UnbDroid/Open2017/Codigos/Vision/src/001.png

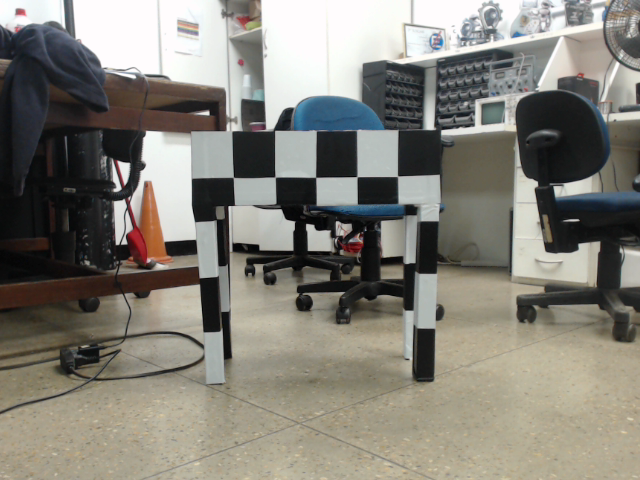
Codigos/Vision/src/001.png
