UnbDroid/Open2017/Codigos/Vision/src/003.png

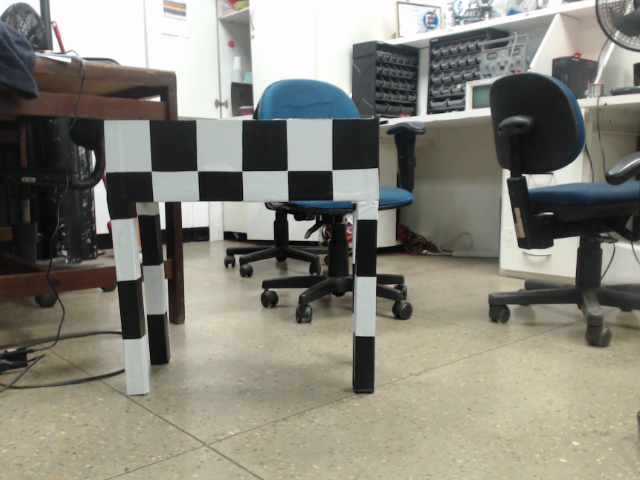
Codigos/Vision/src/003.png
