UnbDroid/Open2017/Codigos/Vision/src/004.png

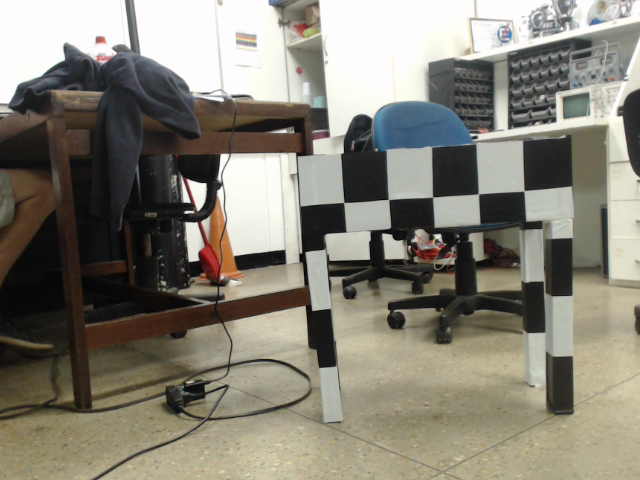
Codigos/Vision/src/004.png
