UnbDroid/Open2017/Codigos/Vision/src/005.png

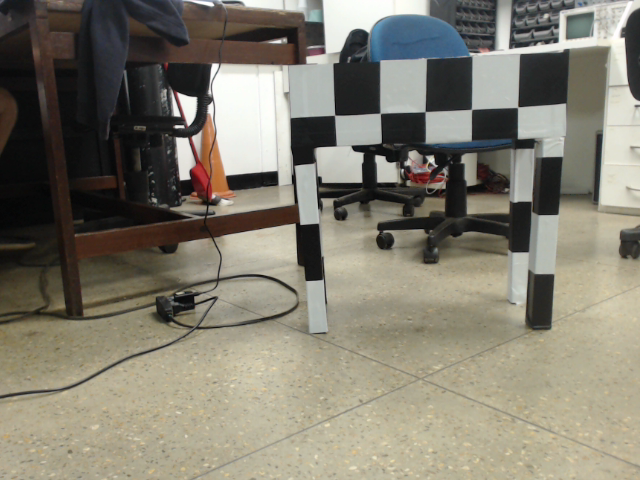
Codigos/Vision/src/005.png
