UnbDroid/Open2017/Codigos/Vision/src/006.png

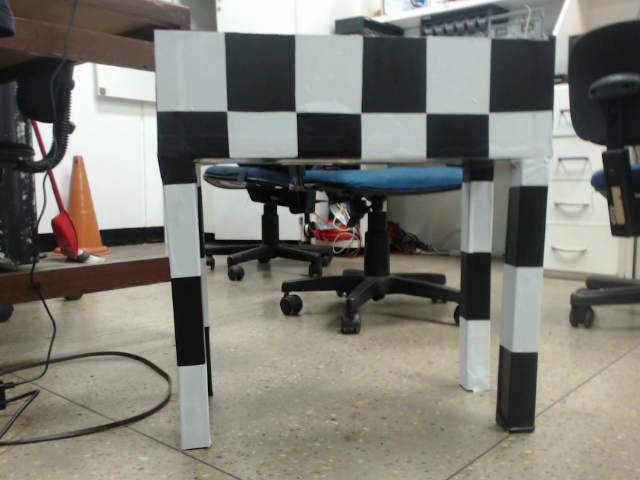
Codigos/Vision/src/006.png
