UnbDroid/Open2017/Codigos/Vision/src/007.png

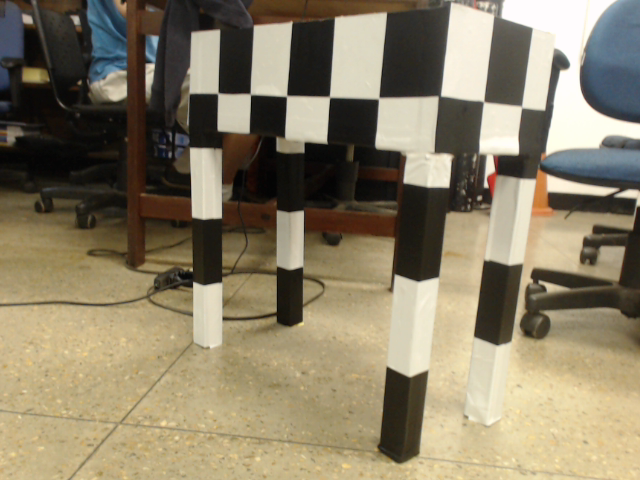
Codigos/Vision/src/007.png
