UnbDroid/Open2017/Codigos/Vision/src/008.png

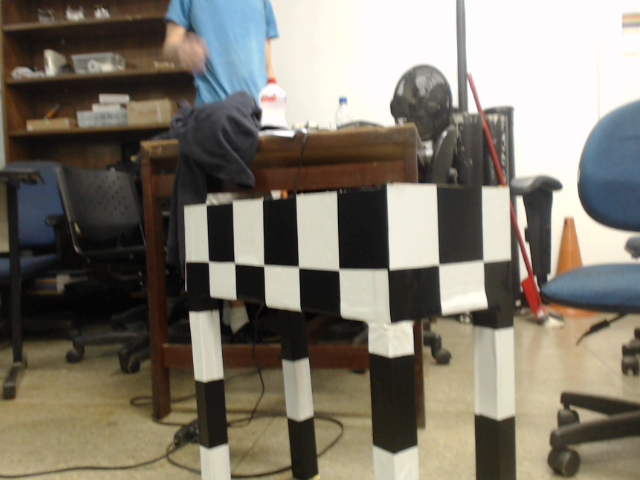
Codigos/Vision/src/008.png
