UnbDroid/Open2017/Codigos/Vision/src/009.png

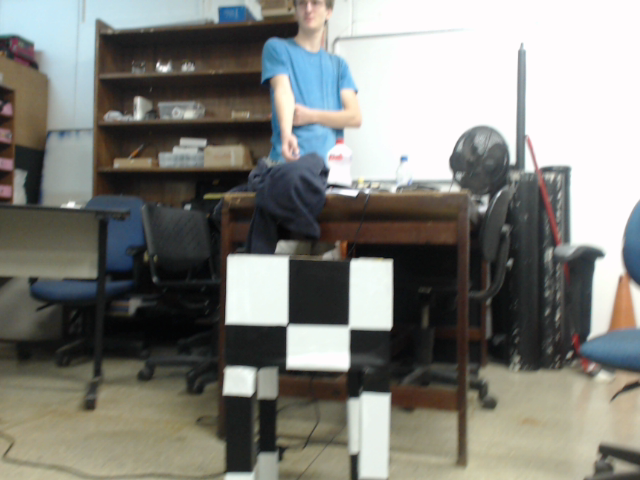
Codigos/Vision/src/009.png
