UnbDroid/Open2017/Codigos/Vision/src/010.png

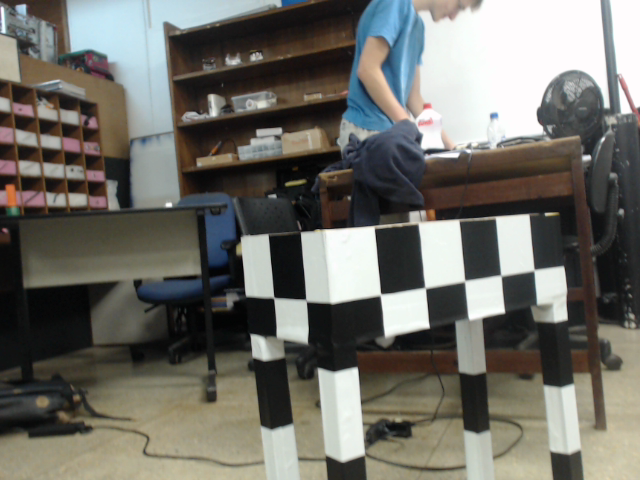
Codigos/Vision/src/010.png
