UnbDroid/Open2017/Codigos/Vision/src/011.png

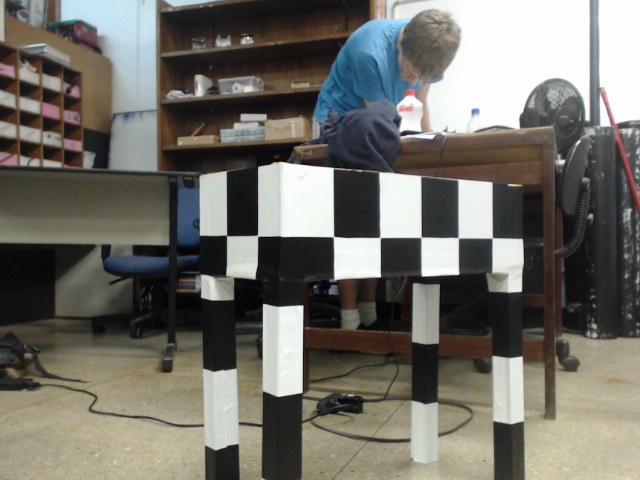
Codigos/Vision/src/011.png
