UnbDroid/Open2017/Codigos/Vision/src/012.png

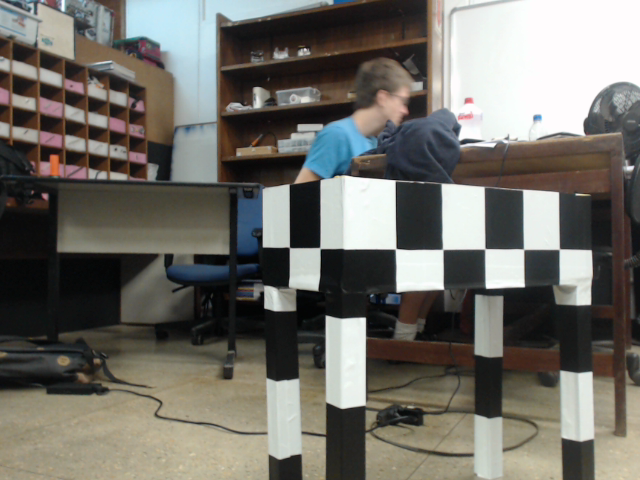
Codigos/Vision/src/012.png
