UnbDroid/Open2017/Codigos/Vision/src/013.png

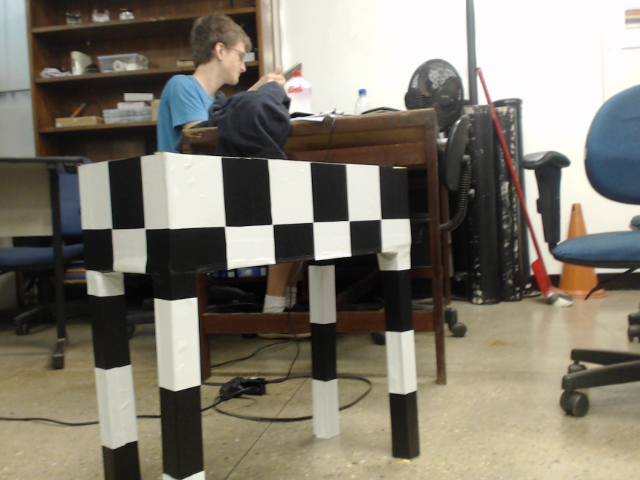
Codigos/Vision/src/013.png
