UnbDroid/Open2017/Codigos/Vision/src/014.png

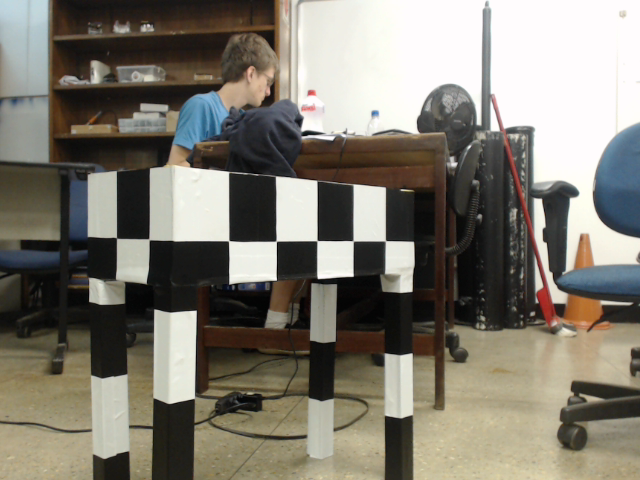
Codigos/Vision/src/014.png
