UnbDroid/Open2017/Codigos/Vision/src/015.png

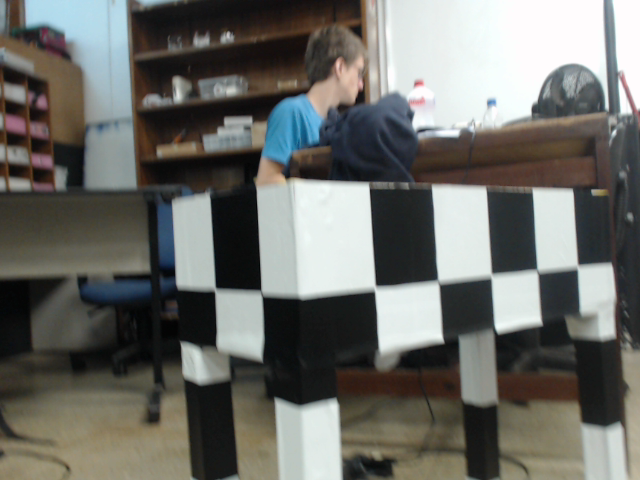
Codigos/Vision/src/015.png
