UnbDroid/Open2017/Codigos/Vision/src/016.png

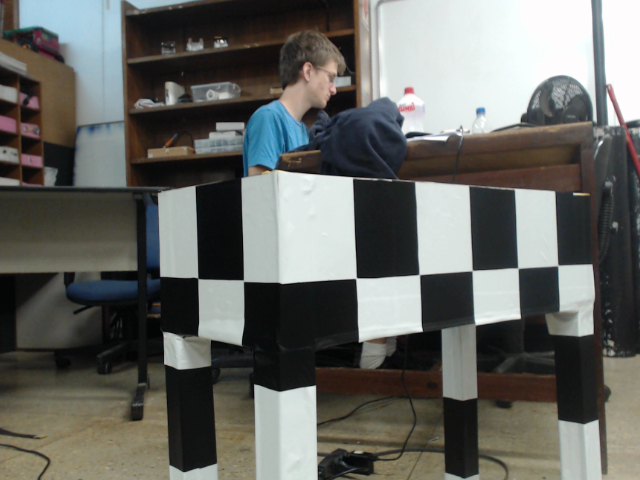
Codigos/Vision/src/016.png
