UnbDroid/Open2017/Codigos/Vision/src/017.png

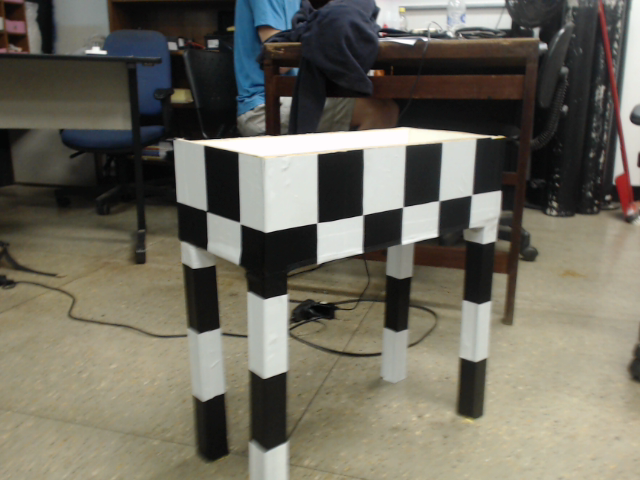
Codigos/Vision/src/017.png
