UnbDroid/Open2017/Codigos/Vision/src/018.png

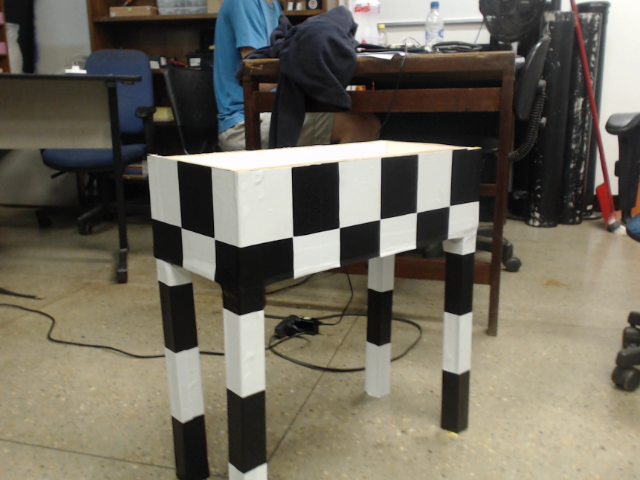
Codigos/Vision/src/018.png
