UnbDroid/Open2017/Codigos/Vision/src/019.png

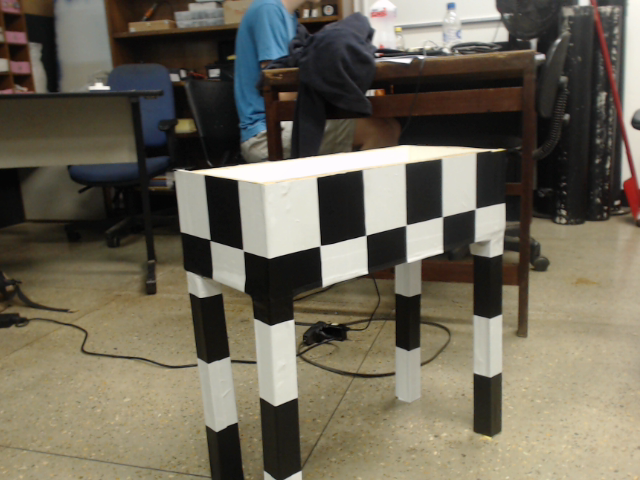
Codigos/Vision/src/019.png
