UnbDroid/Open2017/Codigos/Vision/src/020.png

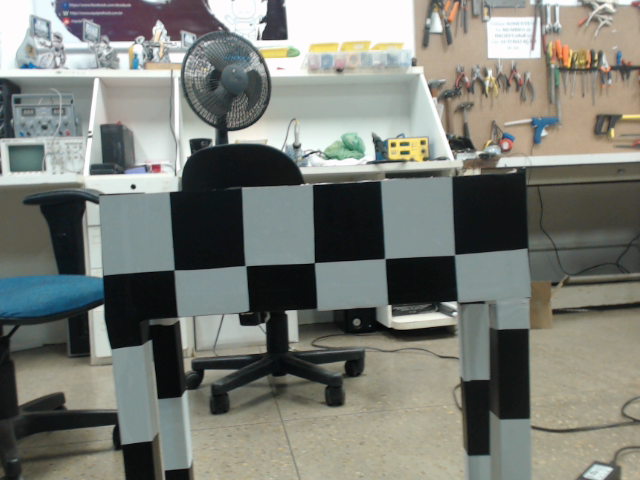
Codigos/Vision/src/020.png
