UnbDroid/Open2017/Codigos/Vision/src/021.png

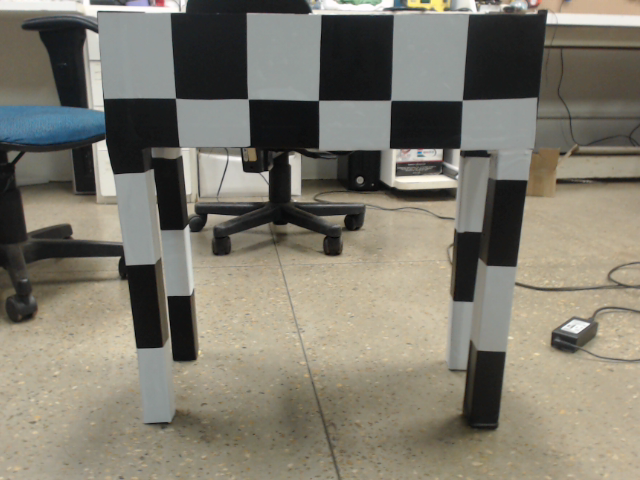
Codigos/Vision/src/021.png
