UnbDroid/Open2017/Codigos/Vision/src/022.png

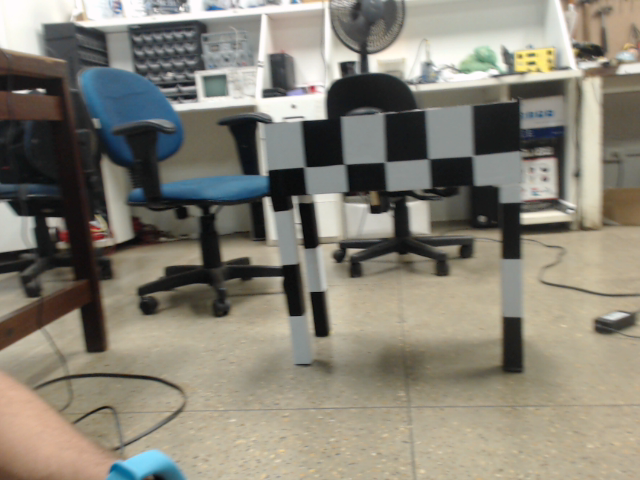
Codigos/Vision/src/022.png
