UnbDroid/Open2017/Codigos/Vision/src/023.png

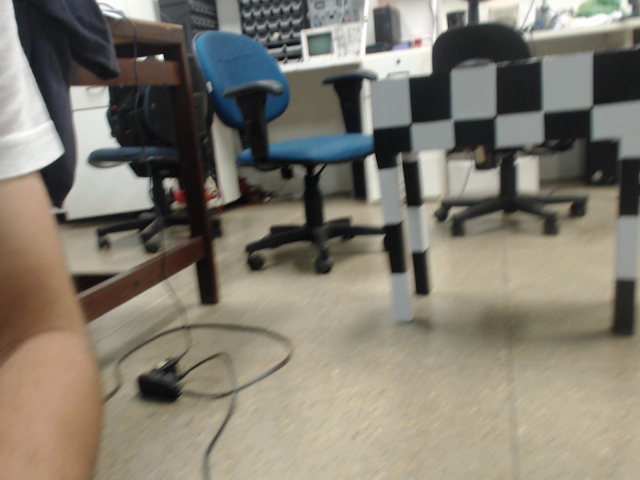
Codigos/Vision/src/023.png
