UnbDroid/Open2017/Codigos/Vision/src/024.png

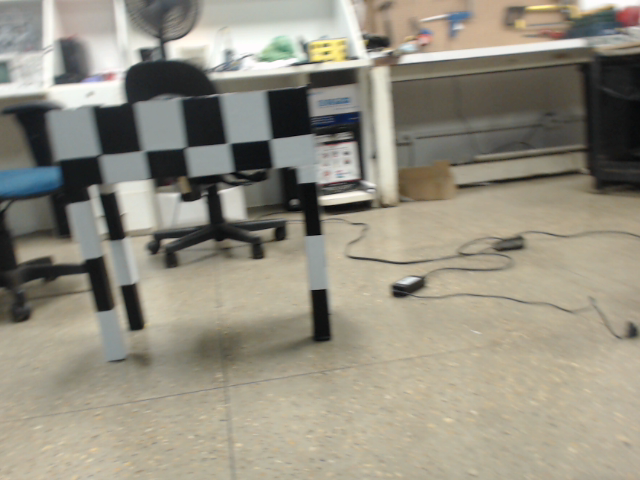
Codigos/Vision/src/024.png
