UnbDroid/Open2017/Codigos/Vision/src/026.png

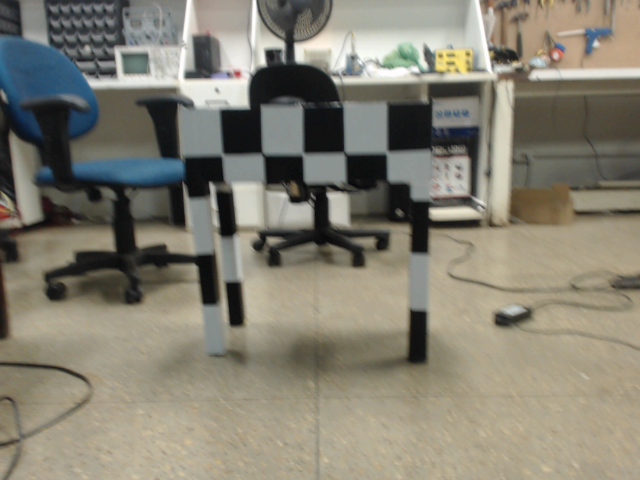
Codigos/Vision/src/026.png
