UnbDroid/Open2017/Codigos/Vision/src/027.png

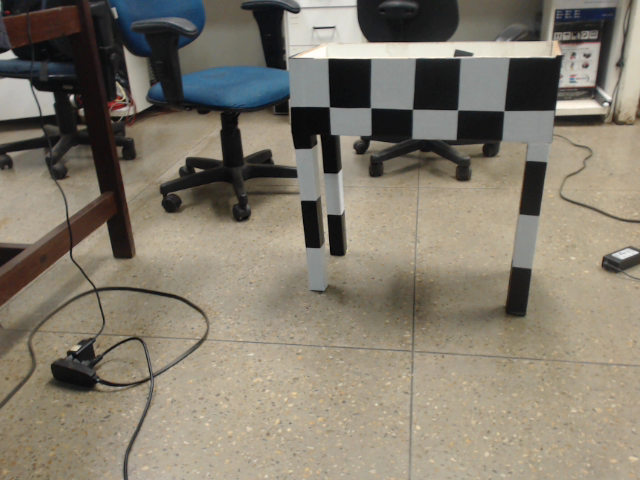
Codigos/Vision/src/027.png
