UnbDroid/Open2017/Codigos/Vision/src/028.png

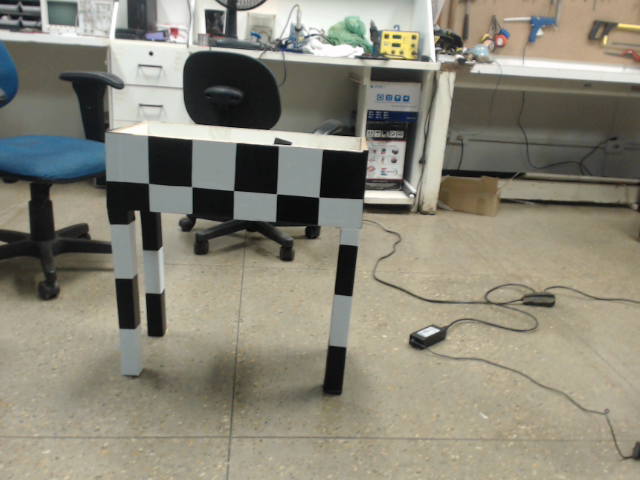
Codigos/Vision/src/028.png
