UnbDroid/Open2017/Codigos/Vision/src/029.png

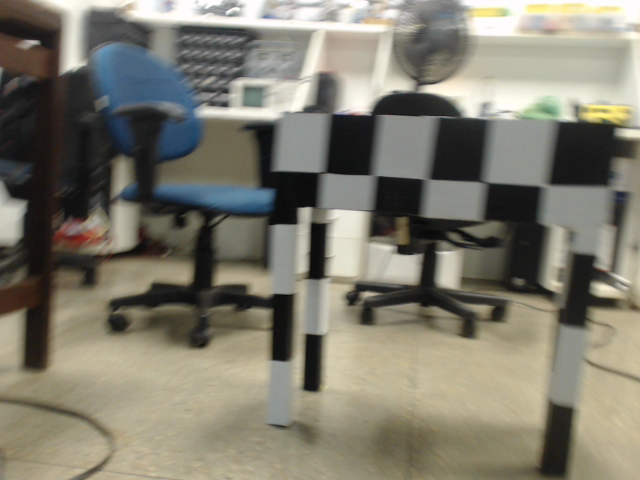
Codigos/Vision/src/029.png
