UnbDroid/Open2017/Codigos/Vision/src/030.png

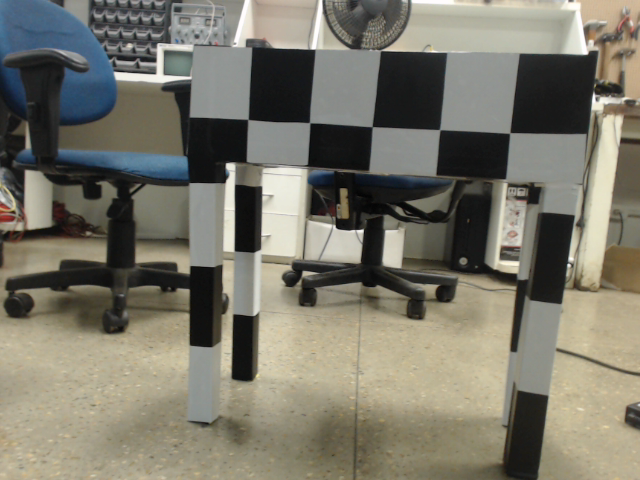
Codigos/Vision/src/030.png
