UnbDroid/Open2017/Codigos/Vision/src/031.png

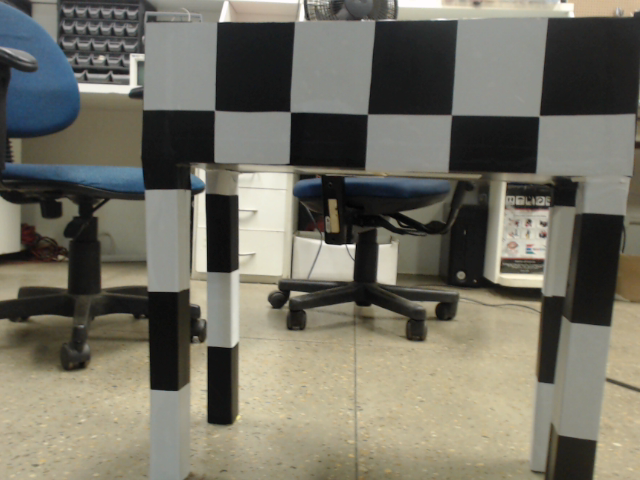
Codigos/Vision/src/031.png
