UnbDroid/Open2017/Codigos/Vision/src/032.png

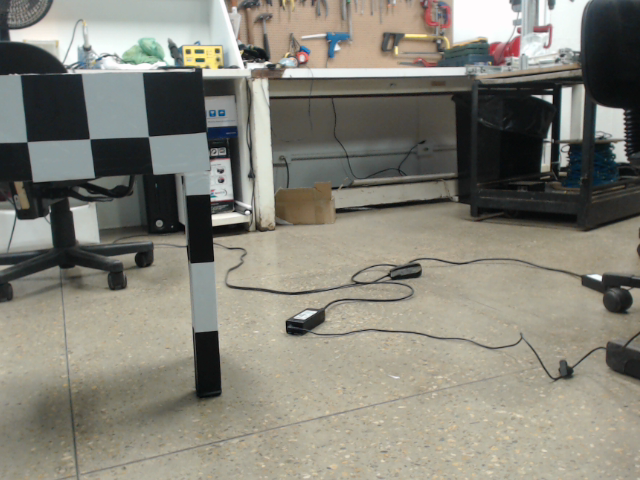
Codigos/Vision/src/032.png
