UnbDroid/Open2017/Codigos/Vision/src/033.png

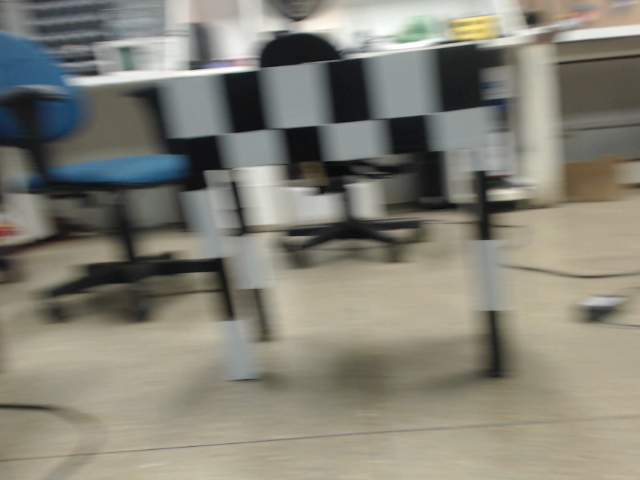
Codigos/Vision/src/033.png
