UnbDroid/Open2017/Codigos/Vision/src/034.png

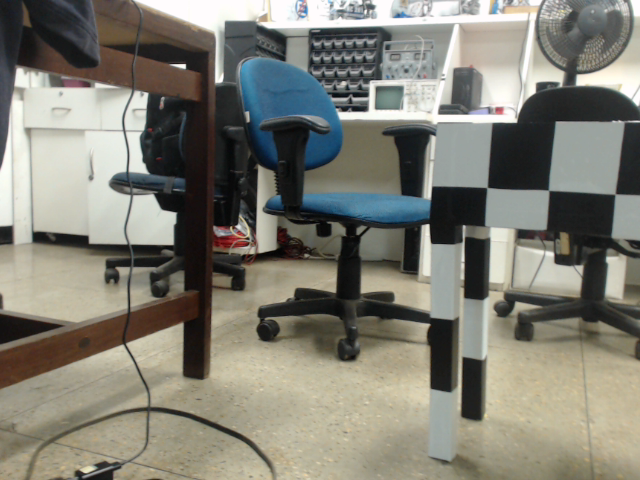
Codigos/Vision/src/034.png
