UnbDroid/Open2017/Codigos/Vision/src/035.png

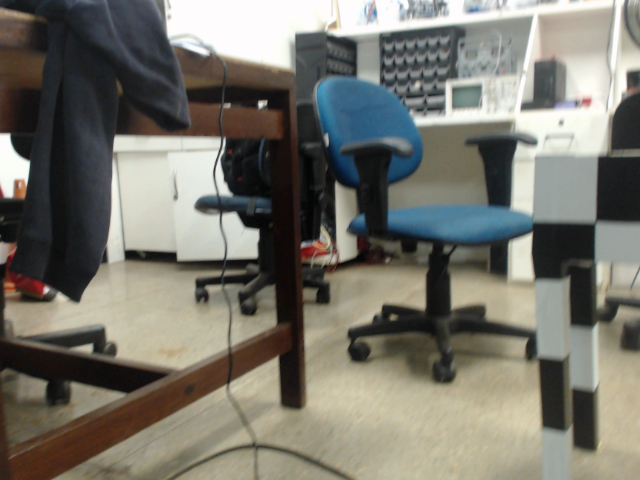
Codigos/Vision/src/035.png
