UnbDroid/Open2017/Codigos/Vision/src/036.png

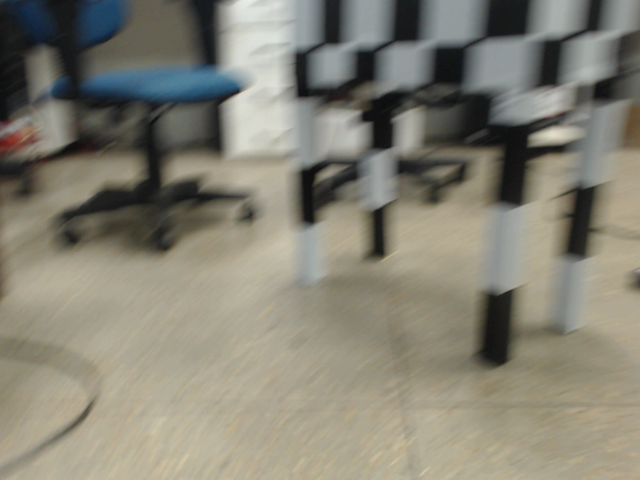
Codigos/Vision/src/036.png
