UnbDroid/Open2017/Codigos/Vision/src/037.png

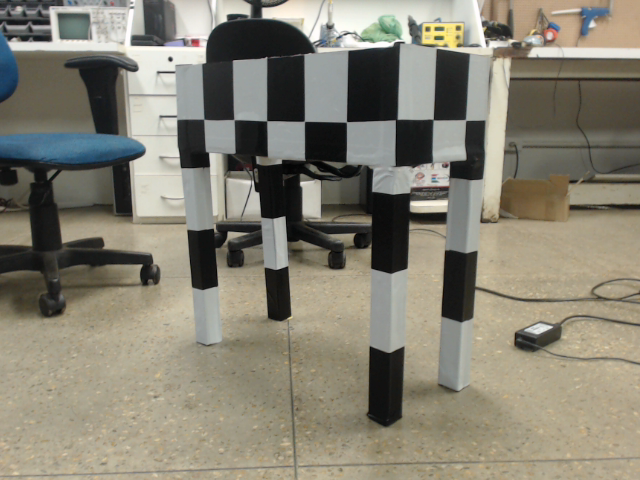
Codigos/Vision/src/037.png
