UnbDroid/Open2017/Codigos/Vision/src/038.png

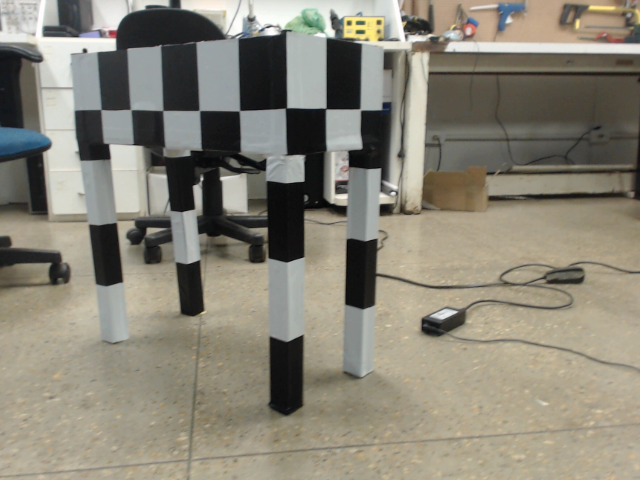
Codigos/Vision/src/038.png
