UnbDroid/Open2017/Codigos/Vision/src/039.png

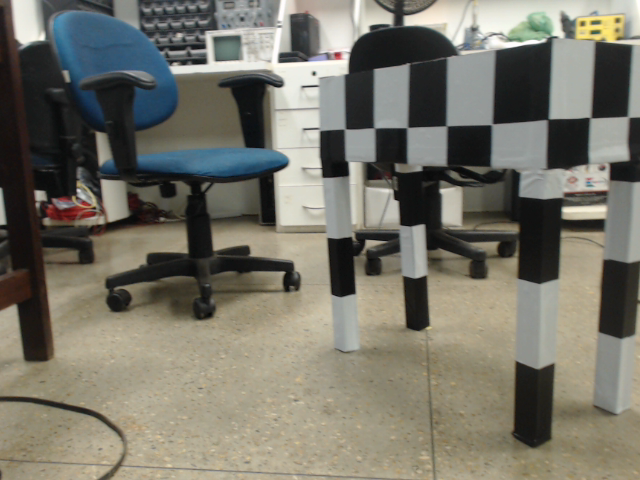
Codigos/Vision/src/039.png
