UnbDroid/Open2017/Codigos/Vision/src/040.png

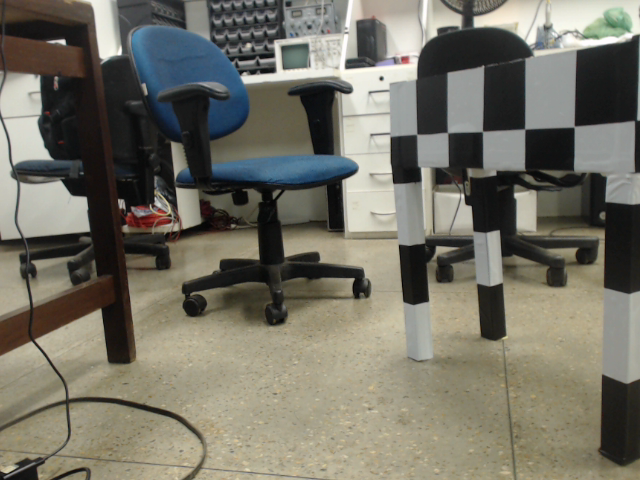
Codigos/Vision/src/040.png
