UnbDroid/Open2017/Codigos/Vision/src/041.png

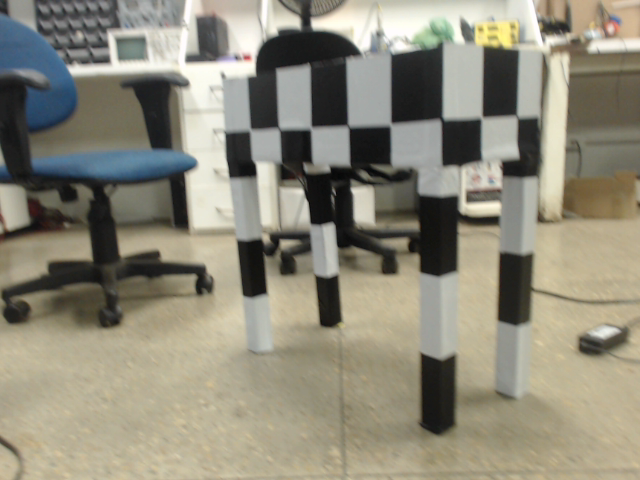
Codigos/Vision/src/041.png
