UnbDroid/Open2017/Codigos/Vision/src/042.png

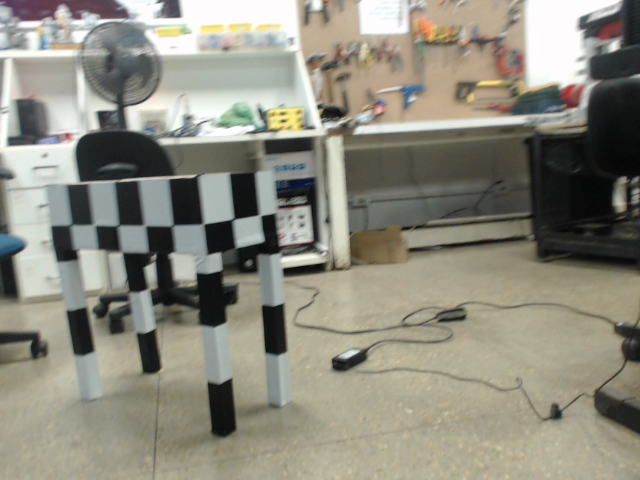
Codigos/Vision/src/042.png
