UnbDroid/Open2017/Codigos/Vision/src/043.png

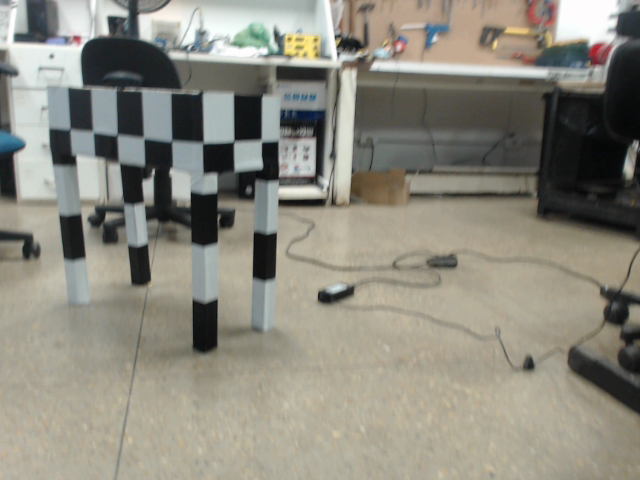
Codigos/Vision/src/043.png
