UnbDroid/Open2017/Codigos/Vision/src/044.png

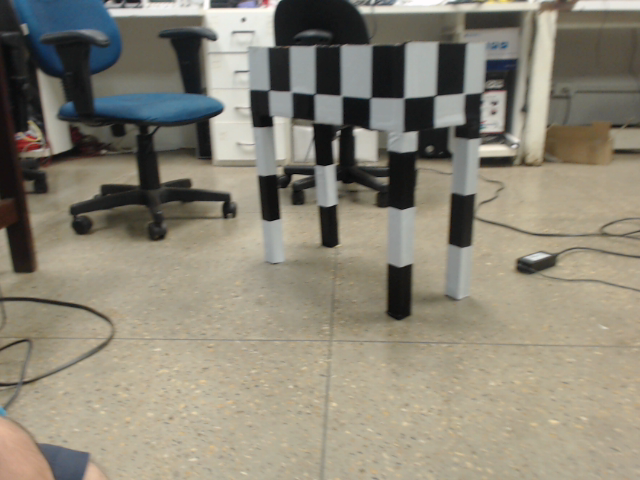
Codigos/Vision/src/044.png
