UnbDroid/Open2017/Codigos/Vision/src/045.png

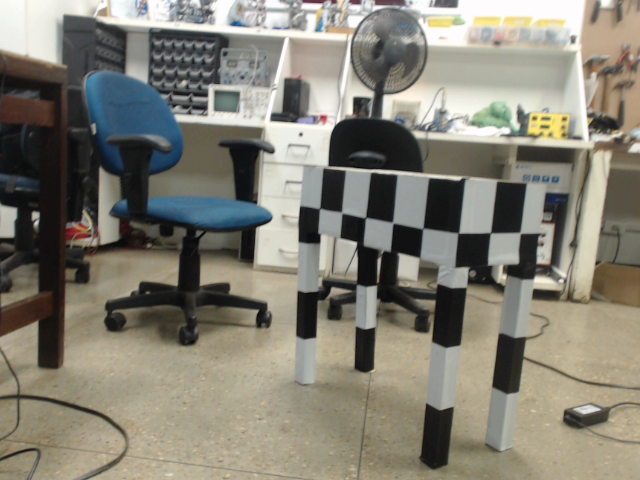
Codigos/Vision/src/045.png
