UnbDroid/Open2017/Codigos/Vision/src/046.png

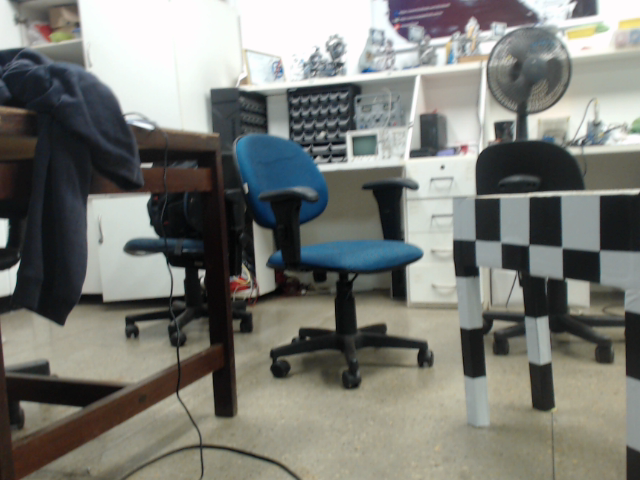
Codigos/Vision/src/046.png
