UnbDroid/Open2017/Codigos/Vision/src/047.png

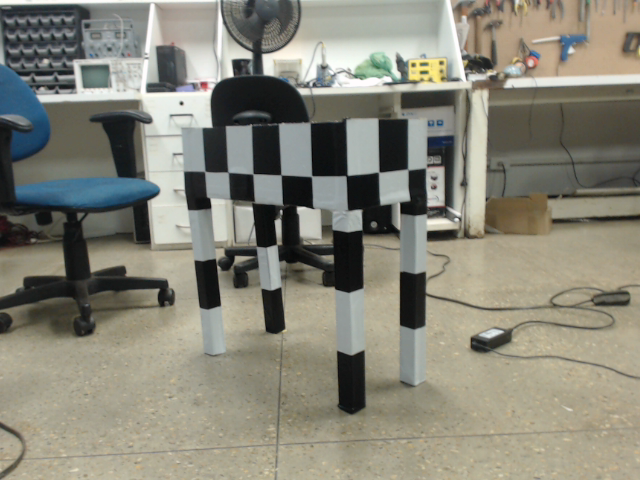
Codigos/Vision/src/047.png
