UnbDroid/Open2017/Codigos/Vision/src/048.png

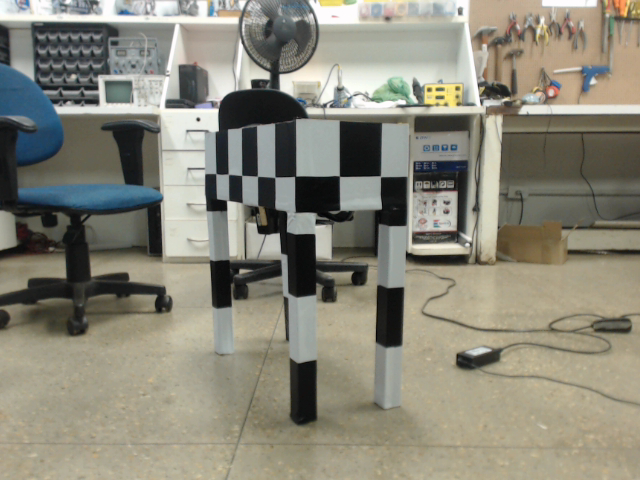
Codigos/Vision/src/048.png
