UnbDroid/Open2017/Codigos/Vision/src/049.png

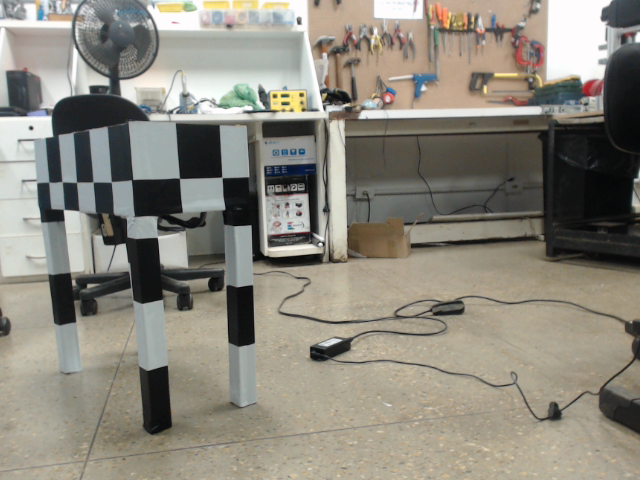
Codigos/Vision/src/049.png
