UnbDroid/Open2017/Codigos/Vision/src/050.png

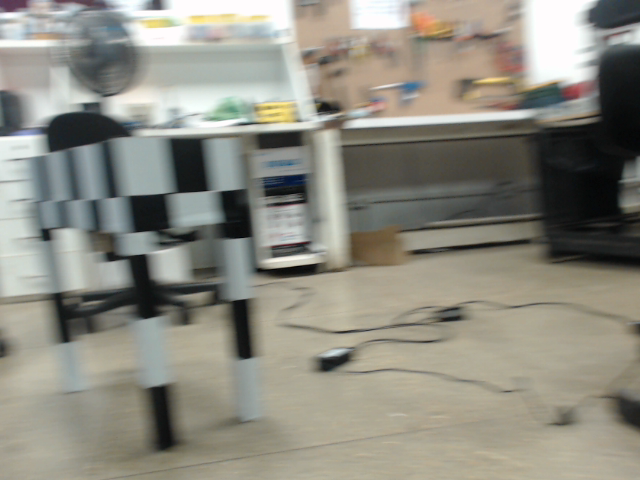
Codigos/Vision/src/050.png
