UnbDroid/Open2017/Codigos/Vision/src/051.png

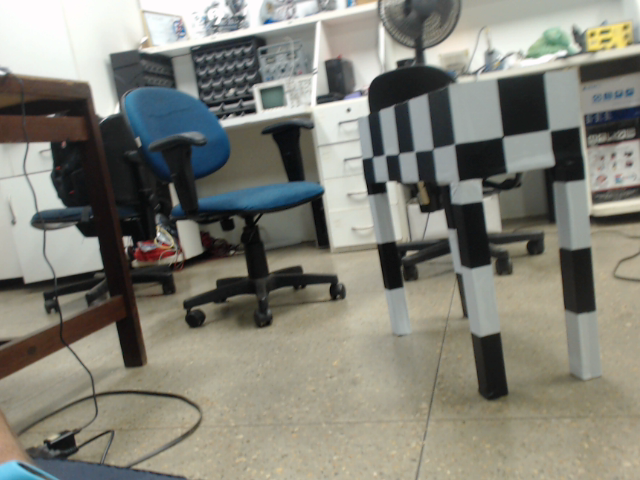
Codigos/Vision/src/051.png
