UnbDroid/Open2017/Codigos/Vision/src/052.png

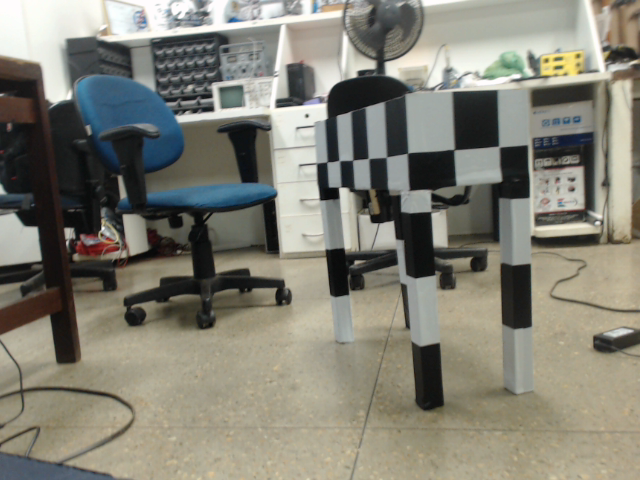
Codigos/Vision/src/052.png
