UnbDroid/Open2017/Codigos/Vision/src/054.png

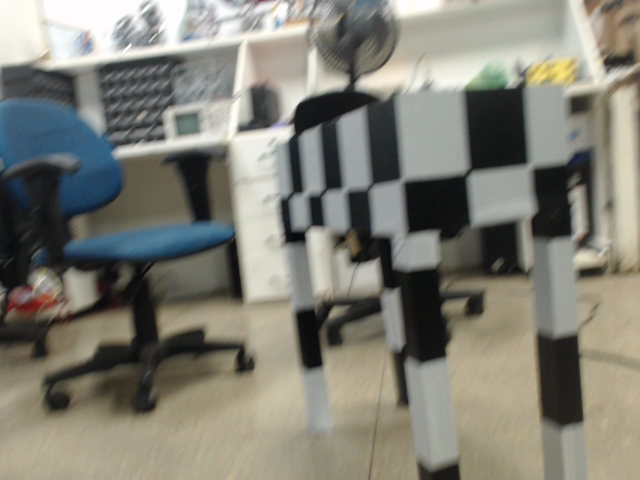
Codigos/Vision/src/054.png
