UnbDroid/Open2017/Codigos/Vision/src/055.png

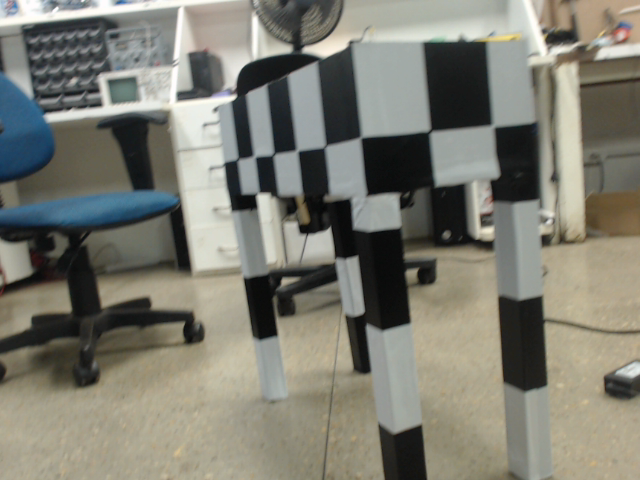
Codigos/Vision/src/055.png
