UnbDroid/Open2017/Codigos/Vision/src/056.png

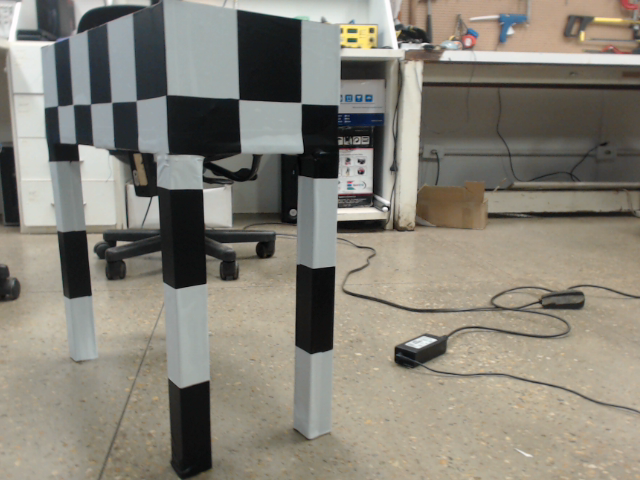
Codigos/Vision/src/056.png
