UnbDroid/Open2017/Codigos/Vision/src/057.png

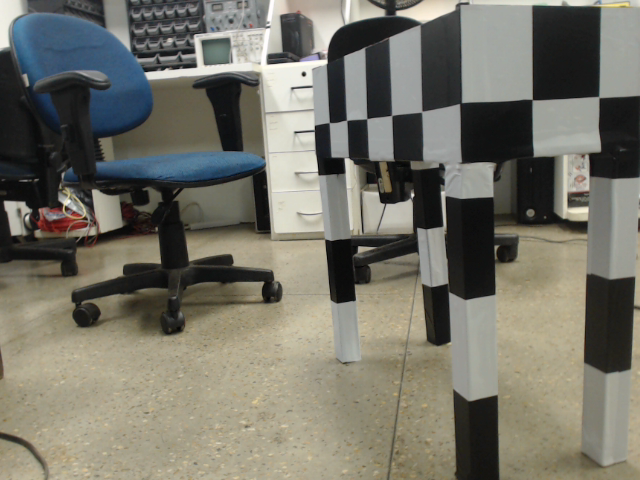
Codigos/Vision/src/057.png
