UnbDroid/Open2017/Codigos/Vision/src/058.png

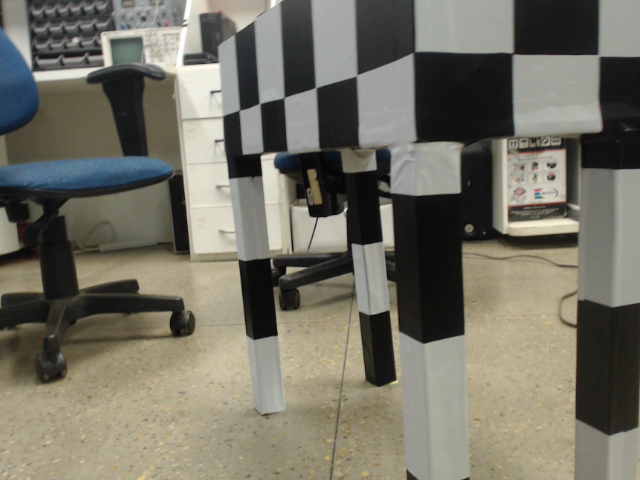
Codigos/Vision/src/058.png
