UnbDroid/Open2017/Codigos/Vision/src/059.png

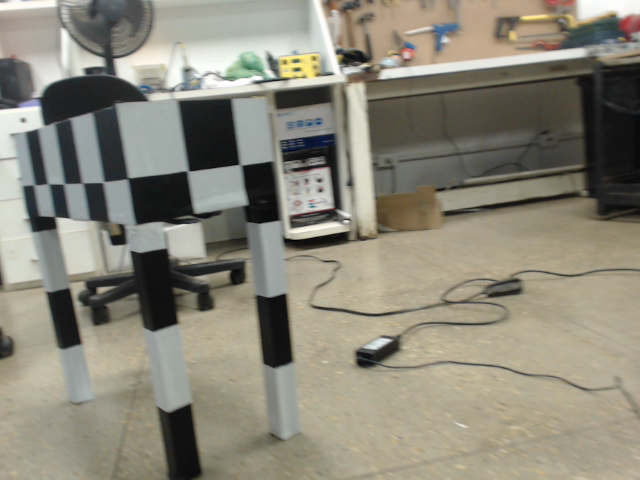
Codigos/Vision/src/059.png
