UnbDroid/Open2017/Codigos/Vision/src/060.png

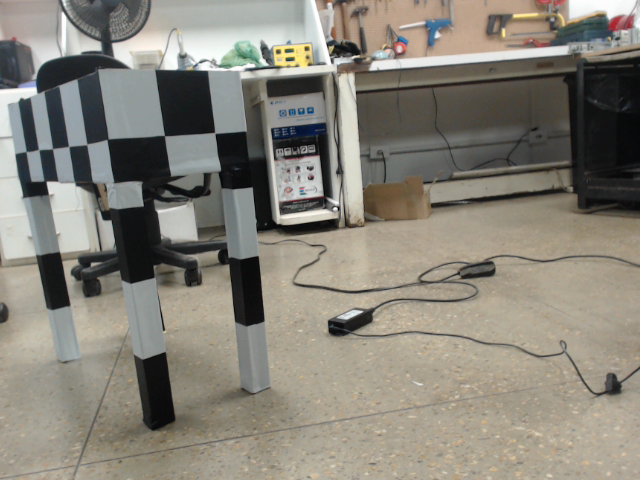
Codigos/Vision/src/060.png
