UnbDroid/Open2017/Codigos/Vision/src/061.png

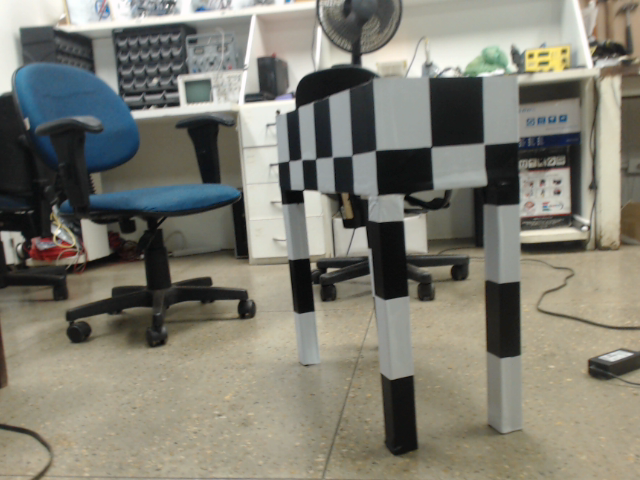
Codigos/Vision/src/061.png
