UnbDroid/Open2017/Codigos/Vision/src/062.png

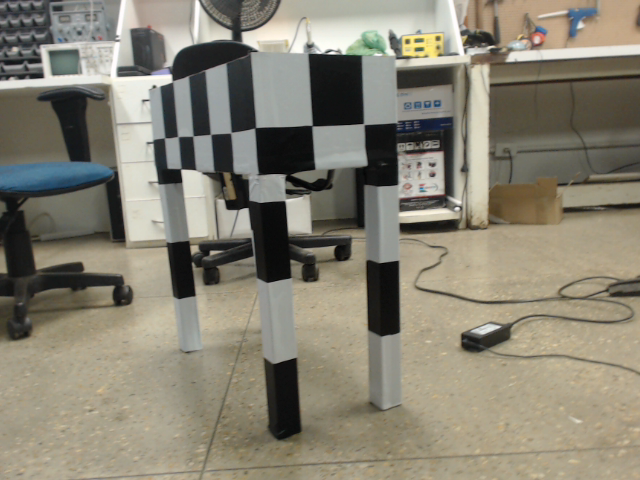
Codigos/Vision/src/062.png
