UnbDroid/Open2017/Codigos/Vision/src/063.png

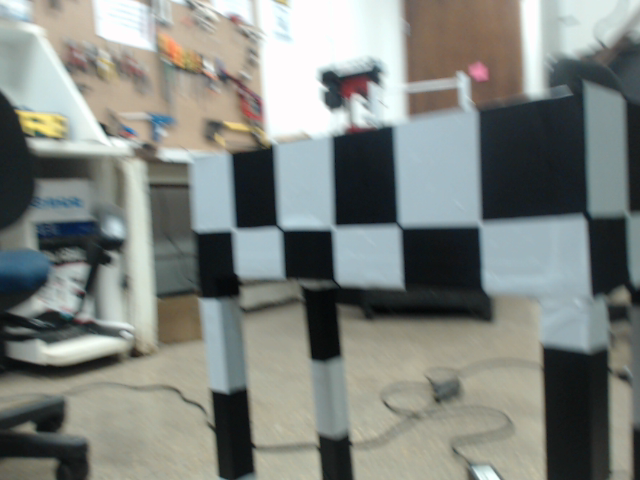
Codigos/Vision/src/063.png
