UnbDroid/Open2017/Codigos/Vision/src/064.png

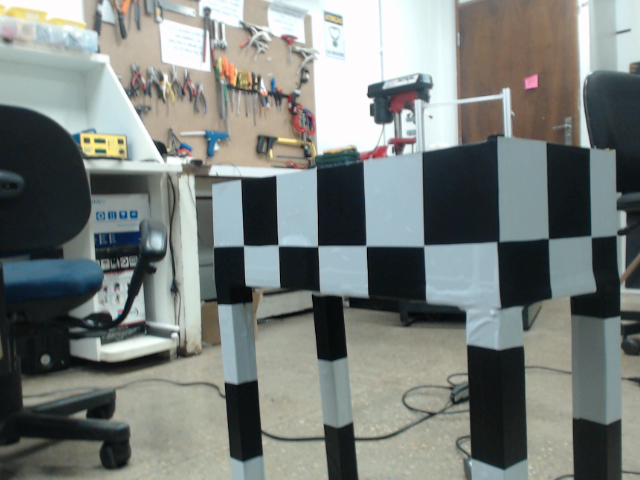
Codigos/Vision/src/064.png
