UnbDroid/Open2017/Codigos/Vision/src/065.png

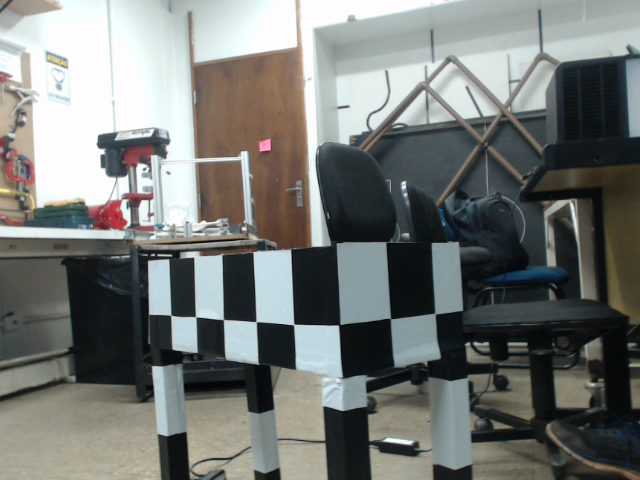
Codigos/Vision/src/065.png
