UnbDroid/Open2017/Codigos/Vision/src/066.png

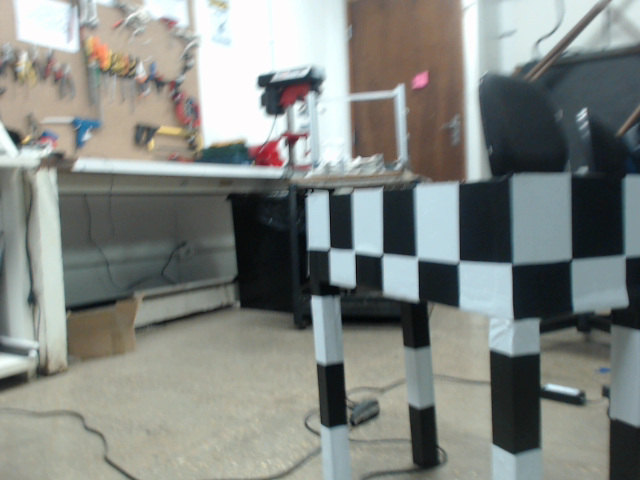
Codigos/Vision/src/066.png
