UnbDroid/Open2017/Codigos/Vision/src/067.png

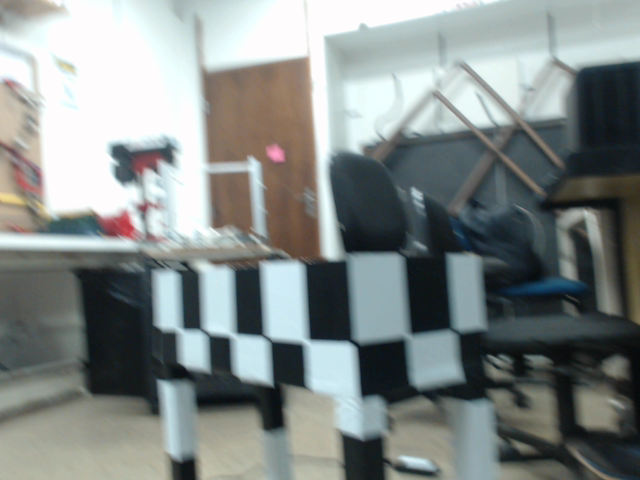
Codigos/Vision/src/067.png
