UnbDroid/Open2017/Codigos/Vision/src/068.png

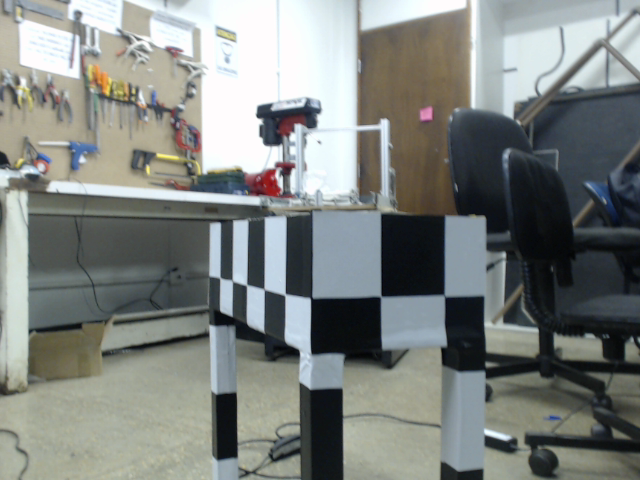
Codigos/Vision/src/068.png
