UnbDroid/Open2017/Codigos/Vision/src/069.png

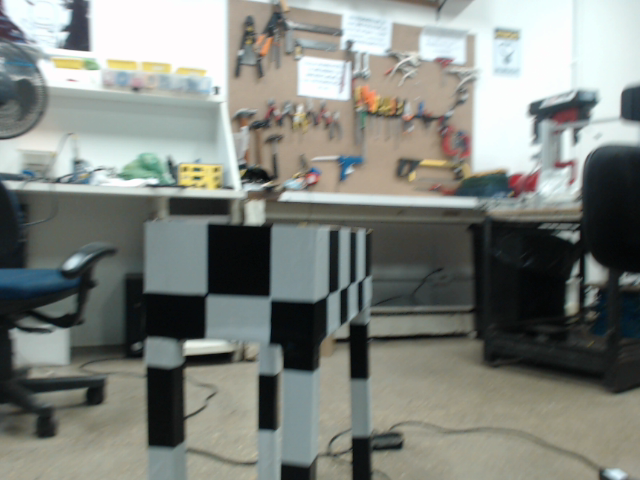
Codigos/Vision/src/069.png
