UnbDroid/Open2017/Codigos/Vision/src/070.png

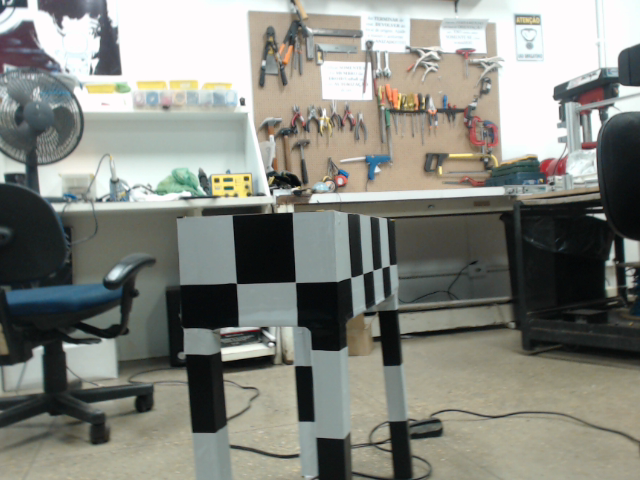
Codigos/Vision/src/070.png
