UnbDroid/Open2017/Codigos/Vision/src/071.png

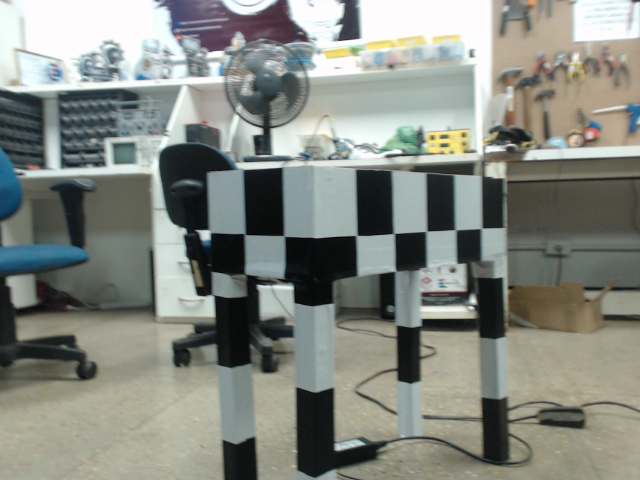
Codigos/Vision/src/071.png
