UnbDroid/Open2017/Codigos/Vision/src/072.png

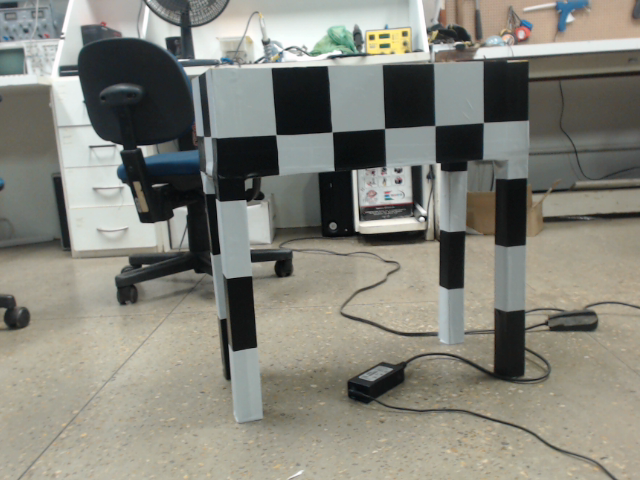
Codigos/Vision/src/072.png
