UnbDroid/Open2017/Codigos/Vision/src/073.png

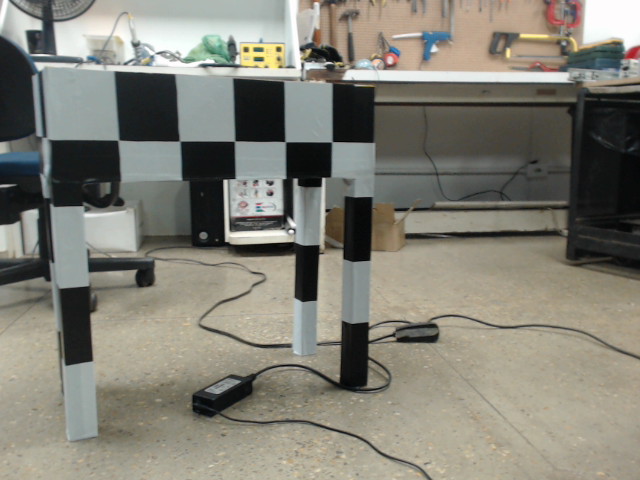
Codigos/Vision/src/073.png
