UnbDroid/Open2017/Codigos/Vision/src/074.png

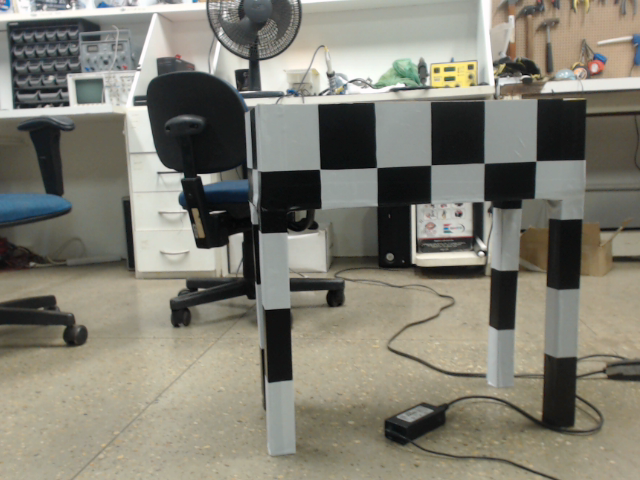
Codigos/Vision/src/074.png
