UnbDroid/Open2017/Codigos/Vision/src/075.png

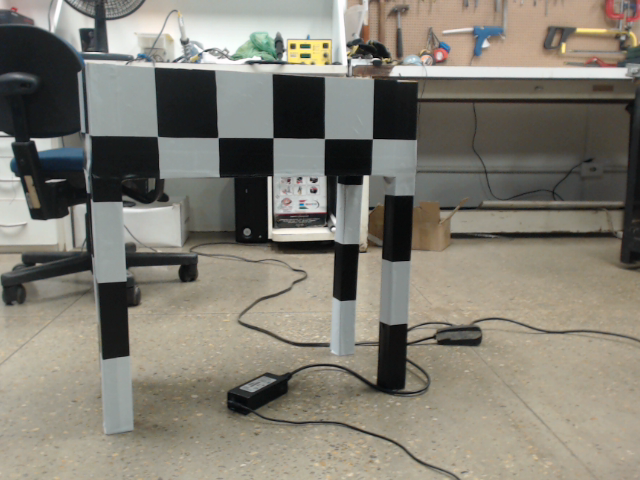
Codigos/Vision/src/075.png
