UnbDroid/Open2017/Codigos/Vision/src/076.png

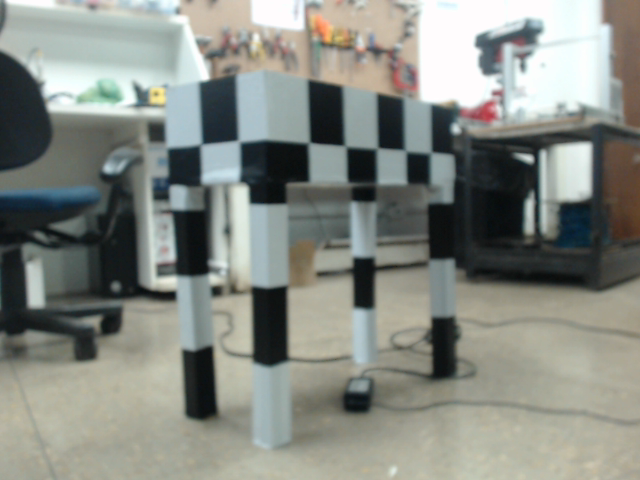
Codigos/Vision/src/076.png
