UnbDroid/Open2017/Codigos/Vision/src/077.png

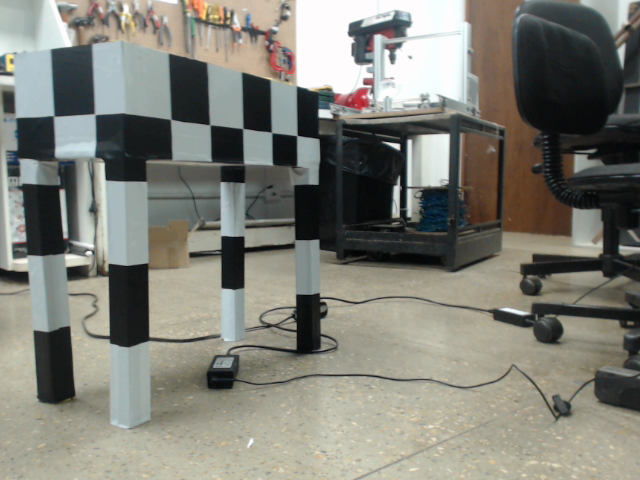
Codigos/Vision/src/077.png
