UnbDroid/Open2017/Codigos/Vision/src/078.png

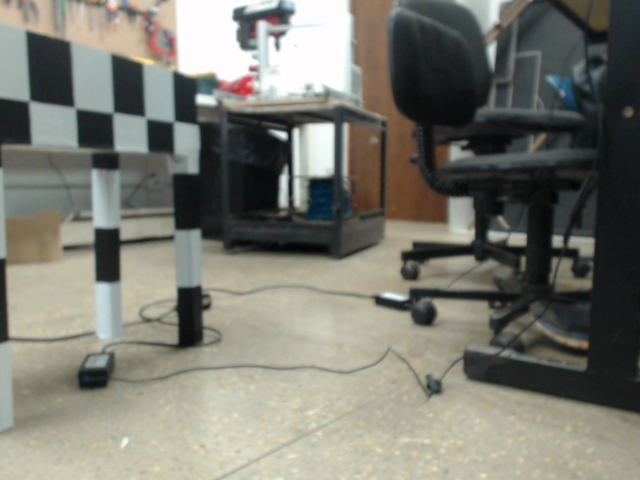
Codigos/Vision/src/078.png
