UnbDroid/Open2017/Codigos/Vision/src/079.png

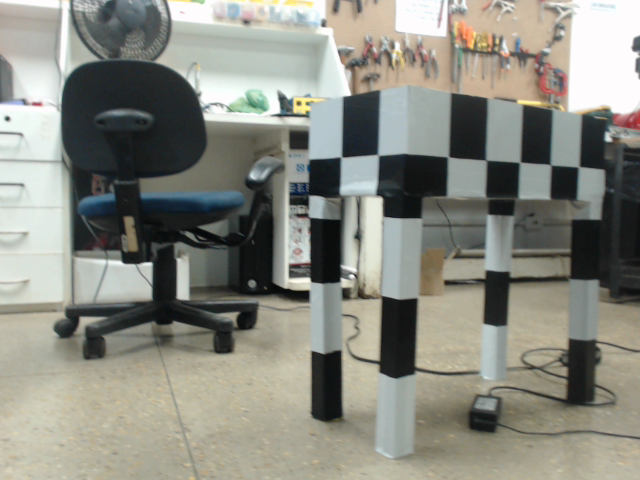
Codigos/Vision/src/079.png
