UnbDroid/Open2017/Codigos/Vision/src/080.png

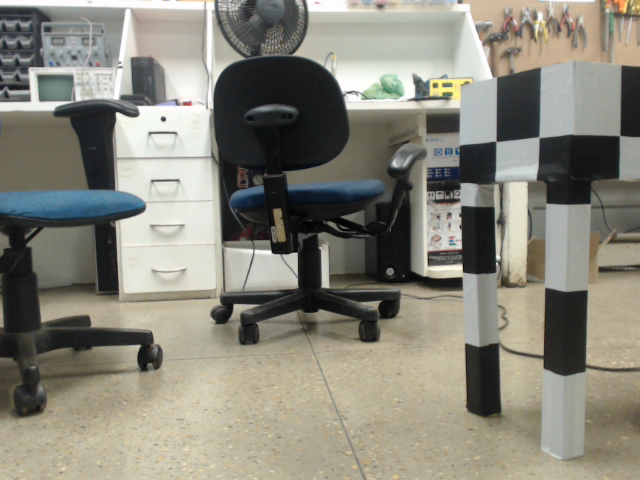
Codigos/Vision/src/080.png
