UnbDroid/Open2017/Codigos/Vision/src/081.png

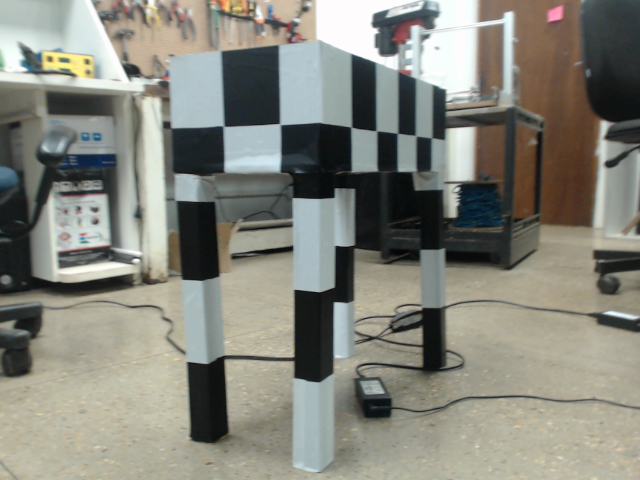
Codigos/Vision/src/081.png
