UnbDroid/Open2017/Codigos/Vision/src/082.png

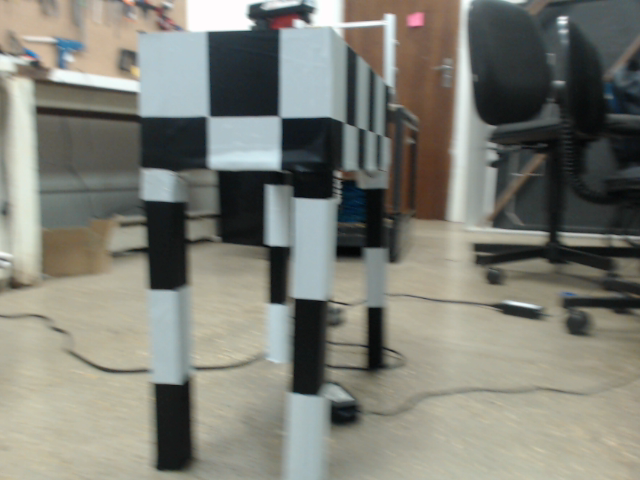
Codigos/Vision/src/082.png
