UnbDroid/Open2017/Codigos/Vision/src/083.png

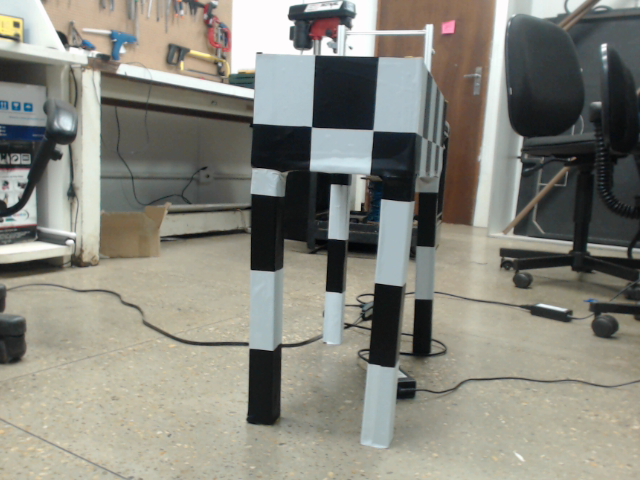
Codigos/Vision/src/083.png
