UnbDroid/Open2017/Codigos/Vision/src/084.png

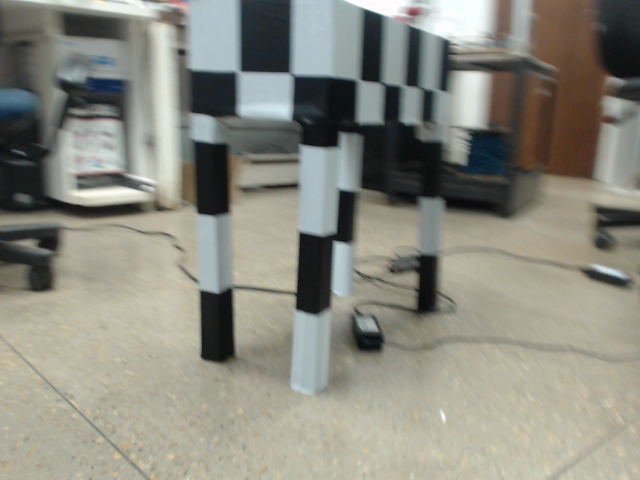
Codigos/Vision/src/084.png
