UnbDroid/Open2017/Codigos/Vision/src/085.png

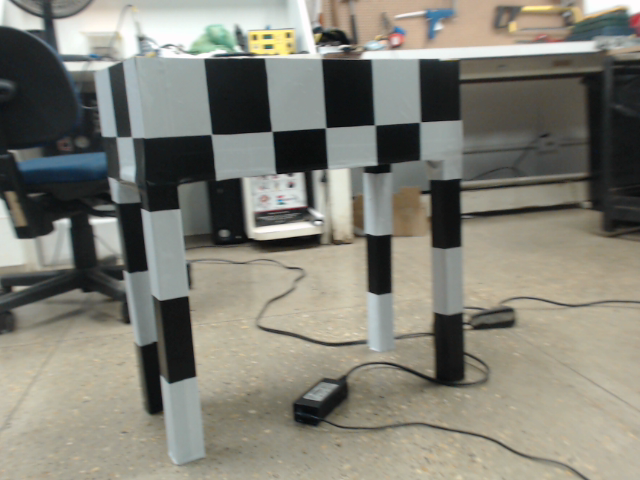
Codigos/Vision/src/085.png
