UnbDroid/Open2017/Codigos/Vision/src/086.png

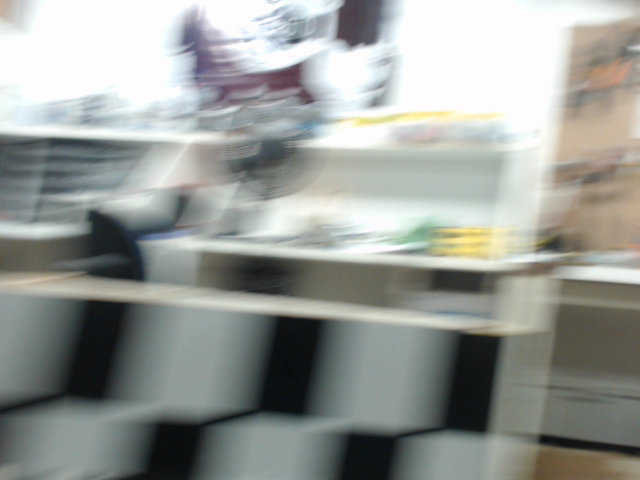
Codigos/Vision/src/086.png
