UnbDroid/Open2017/Codigos/Vision/src/087.png

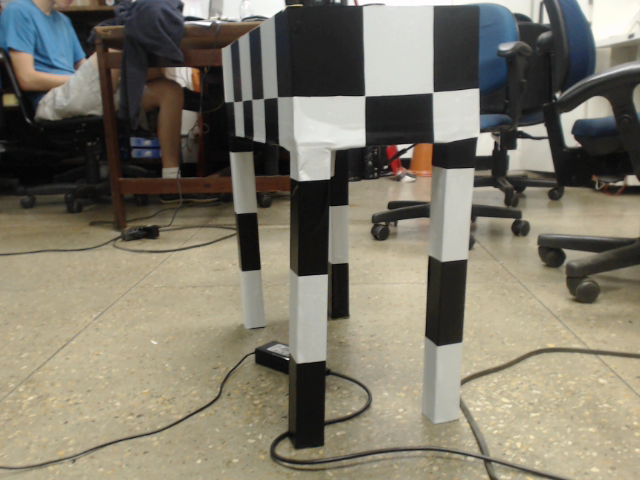
Codigos/Vision/src/087.png
