UnbDroid/Open2017/Codigos/Vision/src/088.png

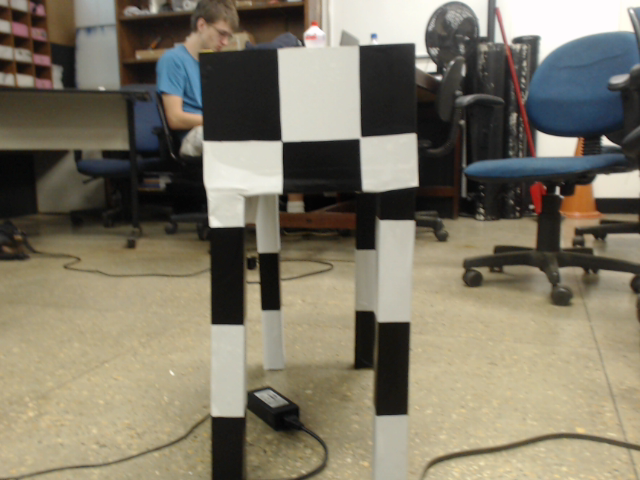
Codigos/Vision/src/088.png
