UnbDroid/Open2017/Codigos/Vision/src/089.png

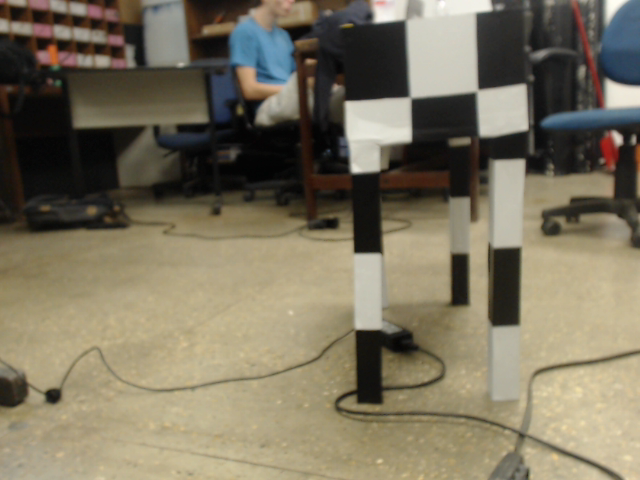
Codigos/Vision/src/089.png
