UnbDroid/Open2017/Codigos/Vision/src/090.png

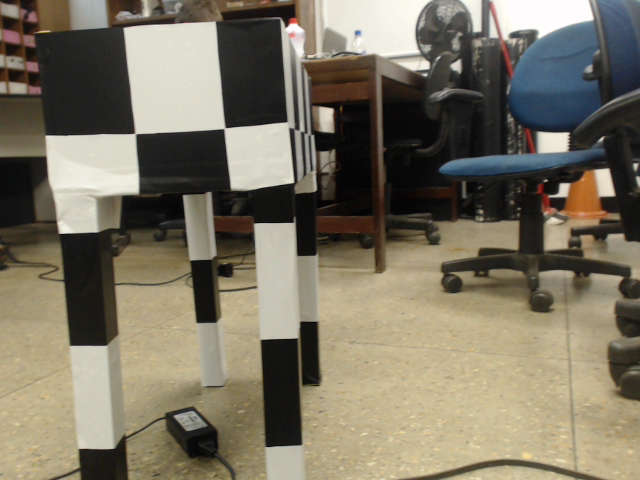
Codigos/Vision/src/090.png
