UnbDroid/Open2017/Codigos/Vision/src/091.png

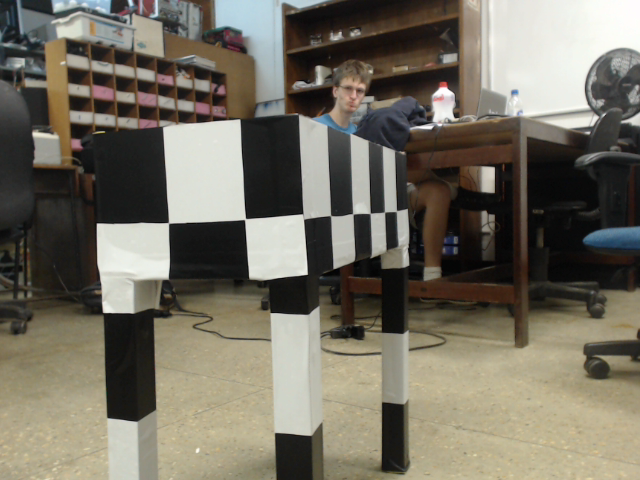
Codigos/Vision/src/091.png
