UnbDroid/Open2017/Codigos/Vision/src/092.png

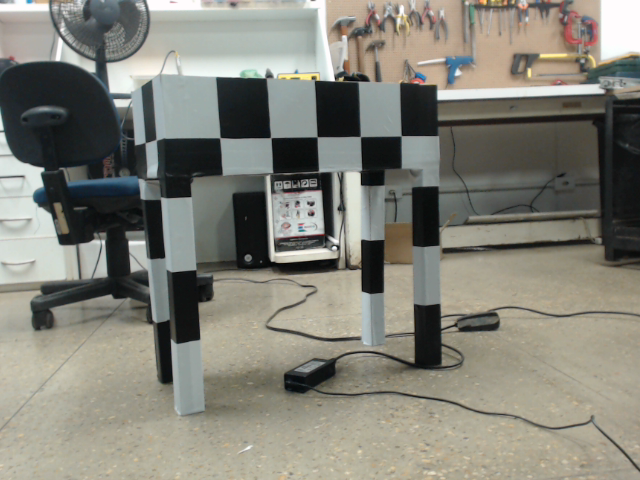
Codigos/Vision/src/092.png
