UnbDroid/Open2017/Codigos/Vision/src/093.png

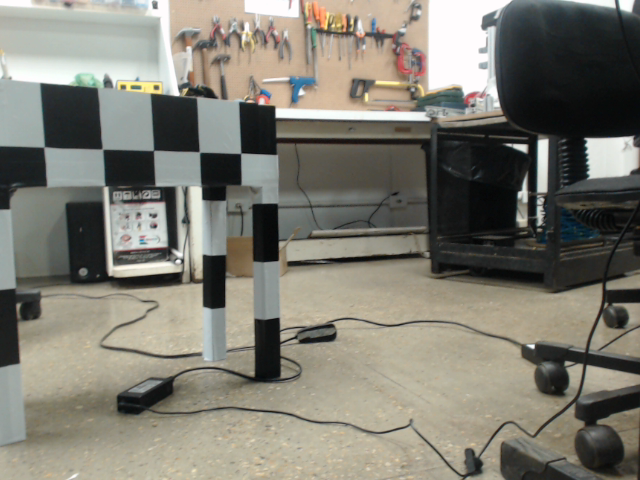
Codigos/Vision/src/093.png
