UnbDroid/Open2017/Codigos/Vision/src/094.png

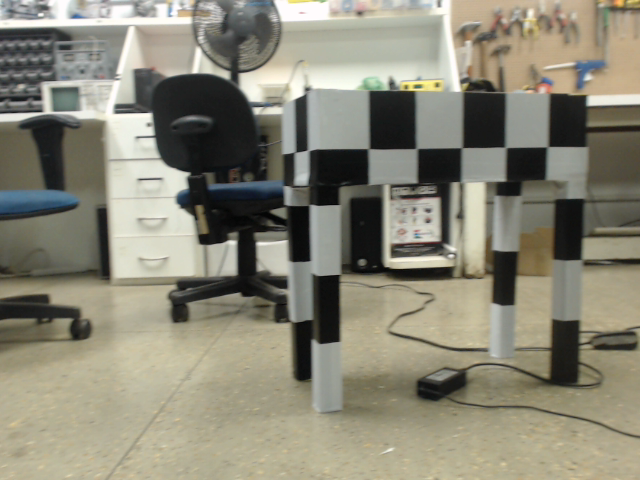
Codigos/Vision/src/094.png
