UnbDroid/Open2017/Codigos/Vision/src/095.png

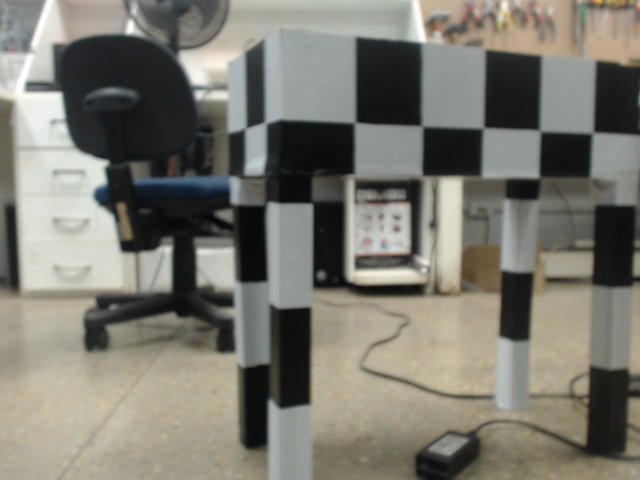
Codigos/Vision/src/095.png
