UnbDroid/Open2017/Codigos/Vision/src/096.png

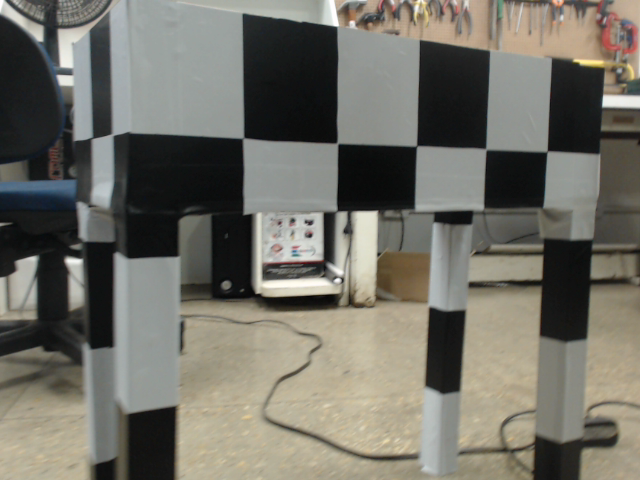
Codigos/Vision/src/096.png
