UnbDroid/Open2017/Codigos/Vision/src/097.png

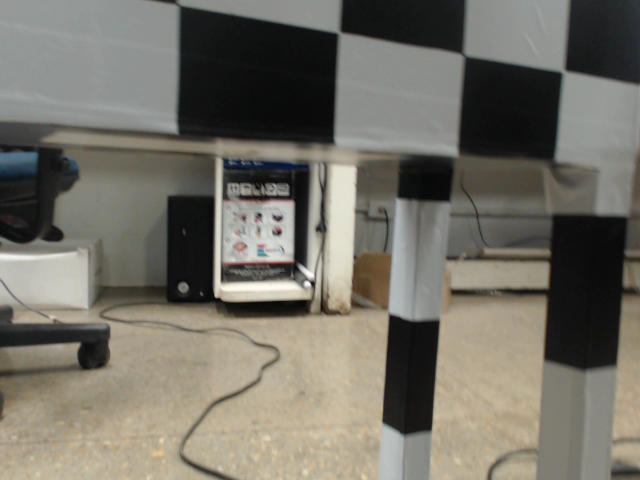
Codigos/Vision/src/097.png
