UnbDroid/Open2017/Codigos/Vision/src/098.png

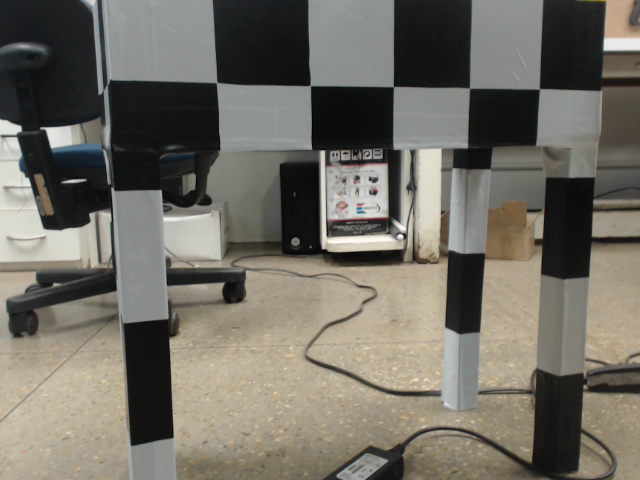
Codigos/Vision/src/098.png
