UnbDroid/Open2017/Codigos/Vision/src/099.png

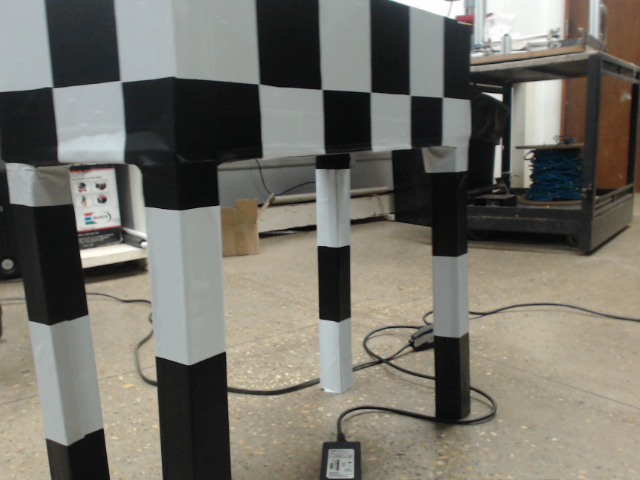
Codigos/Vision/src/099.png
