UnbDroid/Open2017/Codigos/Vision/src/100.png

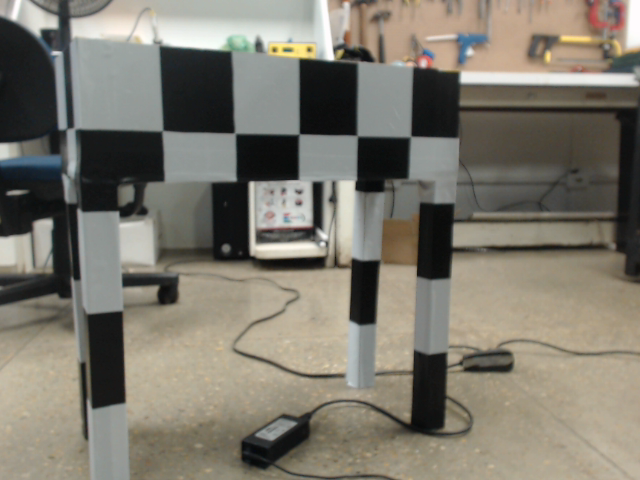
Codigos/Vision/src/100.png
