UnbDroid/Open2017/Codigos/Vision/src/101.jpg

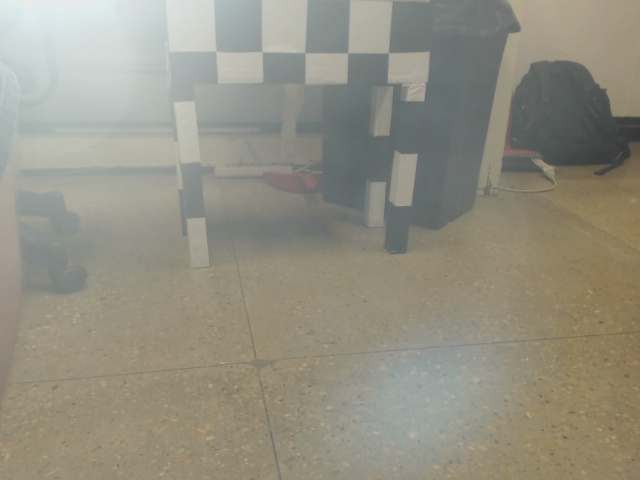
Codigos/Vision/src/101.jpg
