UnbDroid/Open2017/Codigos/Vision/src/102.jpg

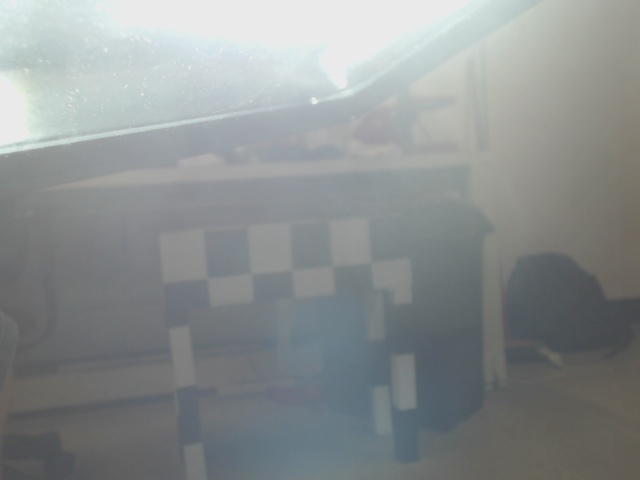
Codigos/Vision/src/102.jpg
