UnbDroid/Open2017/Codigos/Vision/src/103.jpg

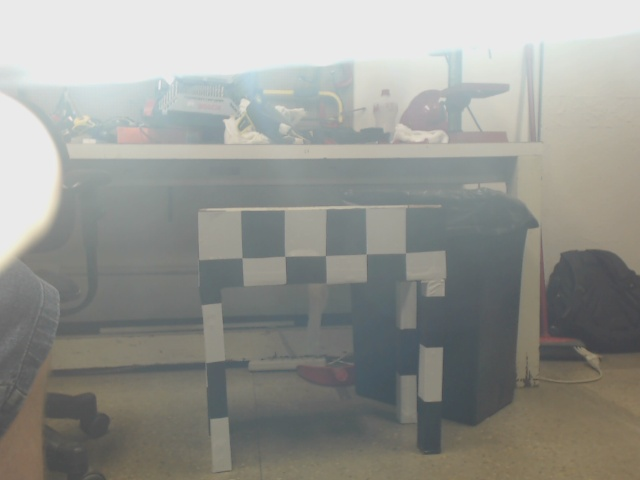
Codigos/Vision/src/103.jpg
