UnbDroid/Open2017/Codigos/Vision/src/104.jpg

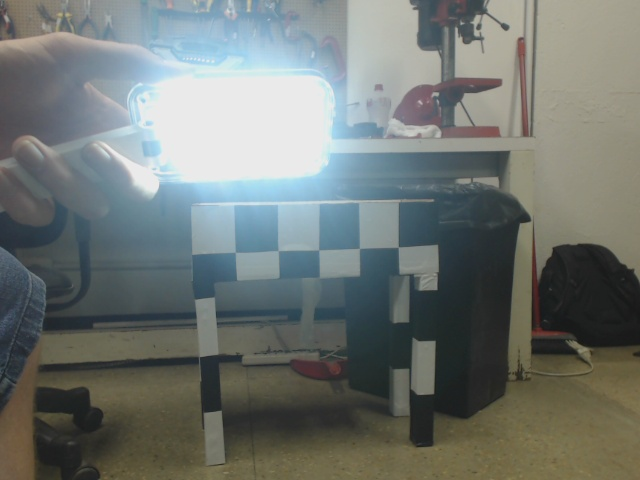
Codigos/Vision/src/104.jpg
