UnbDroid/Open2017/Codigos/Vision/src/106.jpg

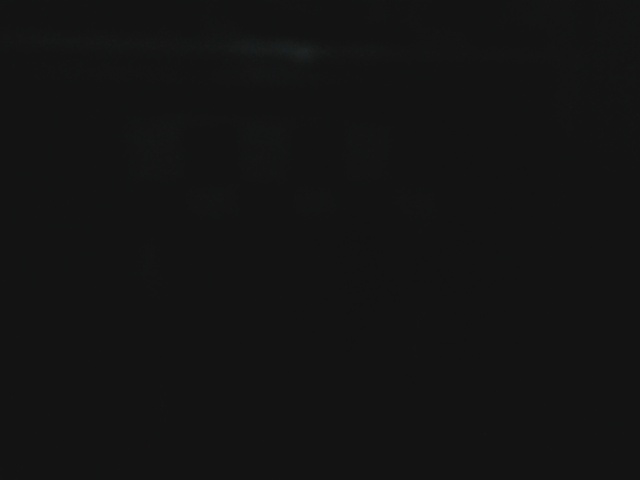
Codigos/Vision/src/106.jpg
