UnbDroid/Open2017/Codigos/Vision/src/107.jpg

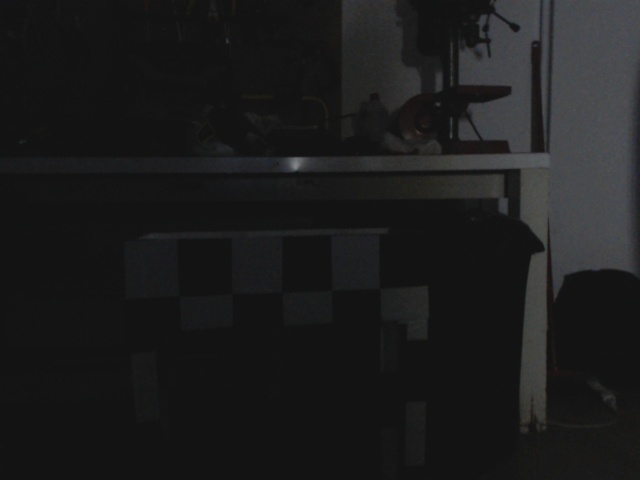
Codigos/Vision/src/107.jpg
