UnbDroid/Open2017/Codigos/Vision/src/108.jpg

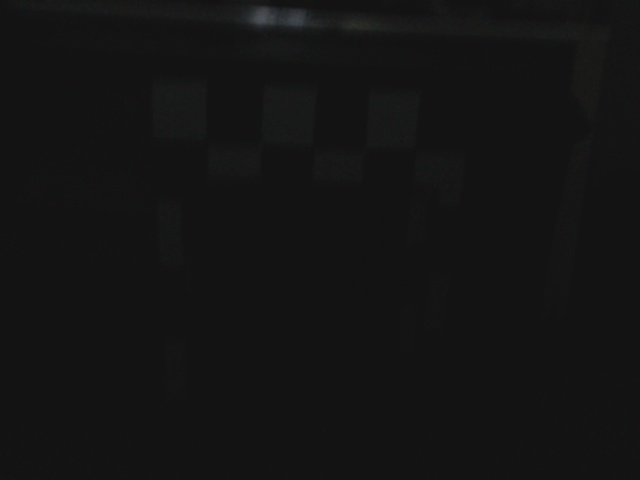
Codigos/Vision/src/108.jpg
