UnbDroid/Open2017/Codigos/Vision/src/109.jpg

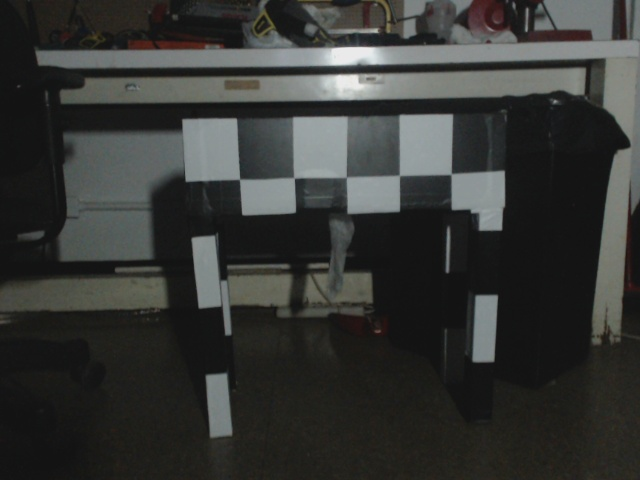
Codigos/Vision/src/109.jpg
