UnbDroid/Open2017/Codigos/Vision/src/110.jpg

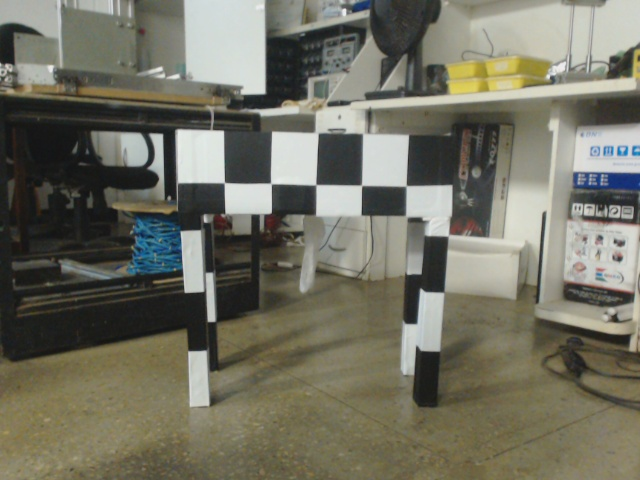
Codigos/Vision/src/110.jpg
