UnbDroid/Open2017/Codigos/Vision/src/111.jpg

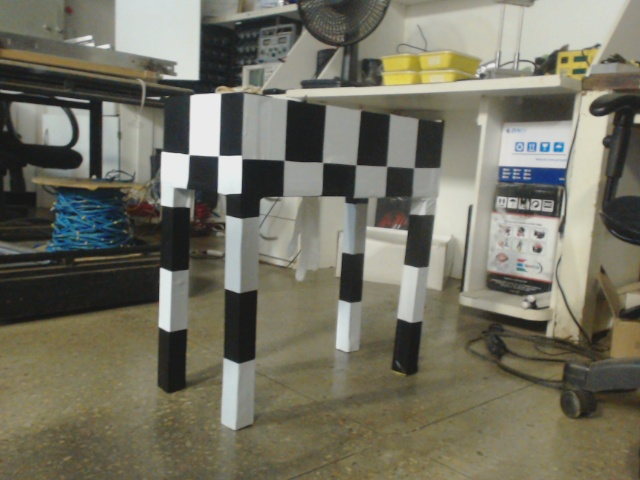
Codigos/Vision/src/111.jpg
