UnbDroid/Open2017/Codigos/Vision/src/112.jpg

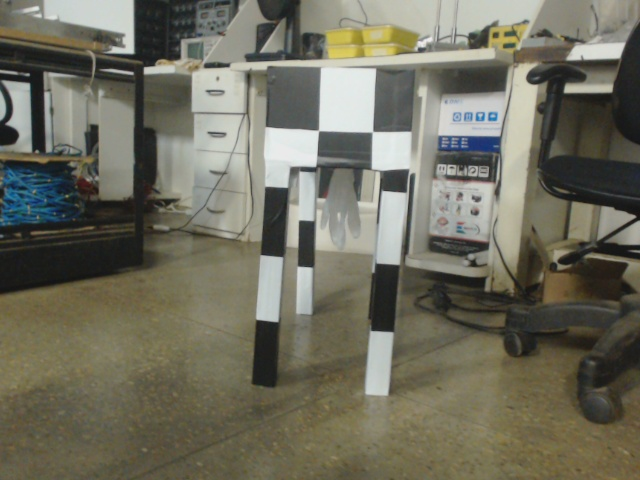
Codigos/Vision/src/112.jpg
