UnbDroid/Open2017/Codigos/Vision/src/113.jpg

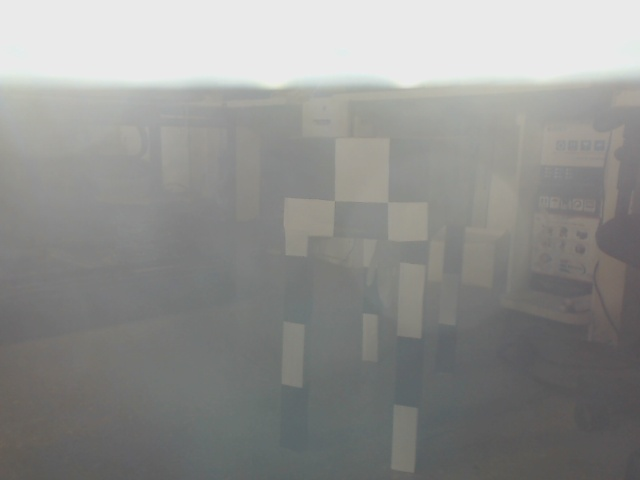
Codigos/Vision/src/113.jpg
