UnbDroid/Open2017/Codigos/Vision/src/114.jpg

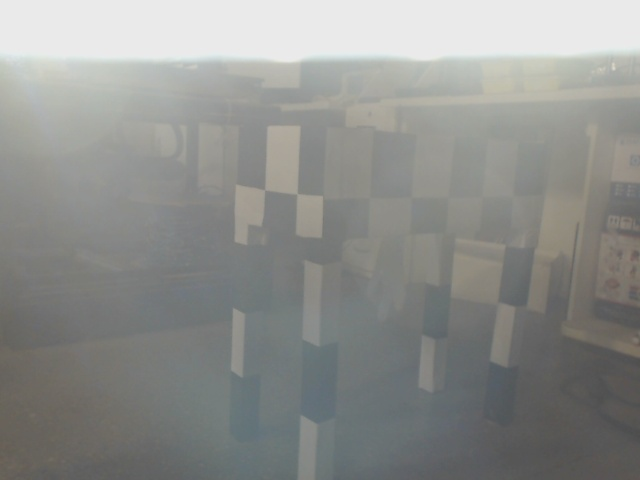
Codigos/Vision/src/114.jpg
