UnbDroid/Open2017/Codigos/mega_open/GarraOpen.h

#ifndef GARRA_H
#define GARRA_H

#include <Arduino.h>
#include "Servo.h"


#define PULSO_CIMA 12
#define PULSO_BAIXO 167

#define ATUADOR_ABRE 75
#define ATUADOR_FECHA 10

#define COTOVELO_FRENTE 170
#define COTOVELO_TRAS 5

#define PRECISAOX 0.022571429 //0.18
#define PRECISAOY 0.02485714 //0.195
#define ORIGEMY 0
#define ORIGEMX 0
#define FREQUENCIA 1000.0

#define QUANTIDADE_MOTORES_GARRA 5

#define MOTOR_PASSO_X 0
#define MOTOR_PASSO_Y 1
#define MOTOR_SERVO_COTOVELO 2
#define MOTOR_SERVO_PULSO 3
#define MOTOR_SERVO_ATUADOR 4

#define ACABOU_GARRA 5

#define NUM_IDEN_GARRA 600


class GarraOpen
{
  public:

    void iniciaServos (int pinCot, int pinPul, int pinAtu);
    void iniciaX (int pin_stp, int pin_dir, int pin_rst, int pin_slp, int pin_ena, int pin_m0, int pin_m1, int pin_m2, int fim_curso, int inicio_curso);
    void iniciaY (int pin_stp, int pin_dir, int pin_rst, int pin_slp, int pin_ena, int pin_m0, int pin_m1, int pin_m2, int fim_curso, int inicio_curso);

    void zeraGarra();

    void movePulso(int pos);
    void moveAtuador(int pos);
    void moveCotovelo(int pos);

    void passoX();
    void passoY();
    void moveX (int pos);
    void moveY (int pos);

    void segueTrajetoria (bool dir);

    void despeja();
    void preparaCopo();
          

    int trataGarra(int id, long long int data);
    bool ehGarra(int id);
    
    void setupGarra();
    
  private:
    Servo cotovelo, pulso, atuador;
    int posX, stpX, dirX, rstX, slpX, enaX, m0X, m1X, m2X, passoAtualX, fimCursoX, inicioCursoX;
    int posY, stpY, dirY, rstY, slpY, enaY, m0Y, m1Y, m2Y, passoAtualY, fimCursoY, inicioCursoY;
    bool posPulso, posAtuador, posCotovelo;
};

#endif
